aydnzn/Development-of-a-Dorsoventral-Ballistocardiographic-Measurement-System/eagle_docs/fsr_board/3.png

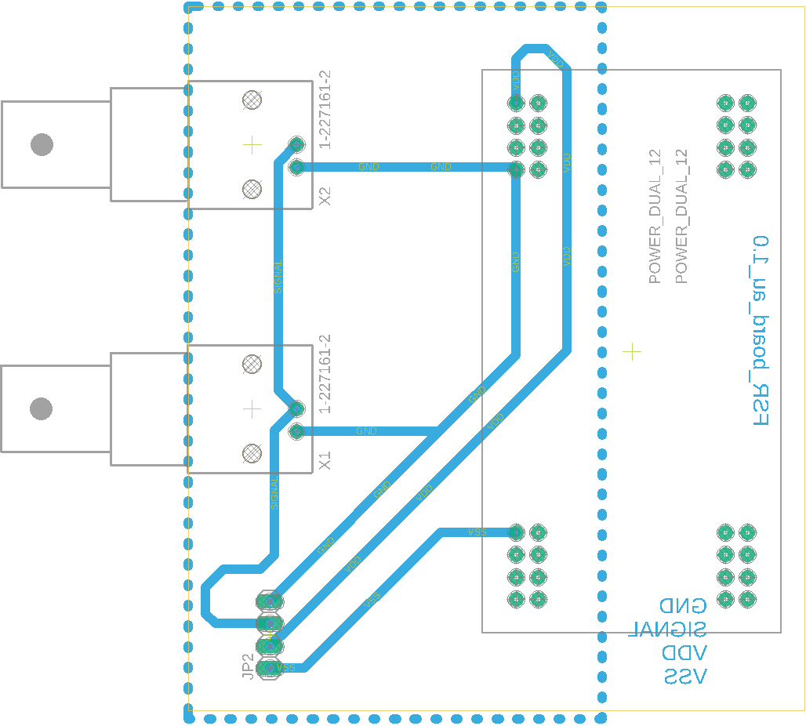
eagle_docs/fsr_board/3.png
