aydnzn/Development-of-a-Dorsoventral-Ballistocardiographic-Measurement-System/eagle_docs/fsr_board/4.png

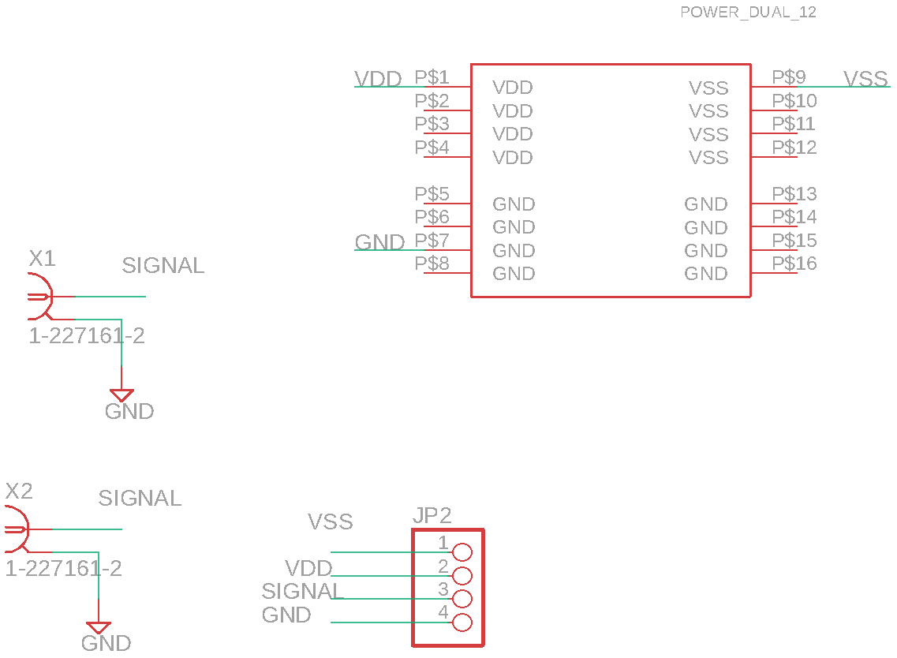
eagle_docs/fsr_board/4.png
