aydnzn/Development-of-a-Dorsoventral-Ballistocardiographic-Measurement-System/eagle_docs/fsr_board/fsr_img.png

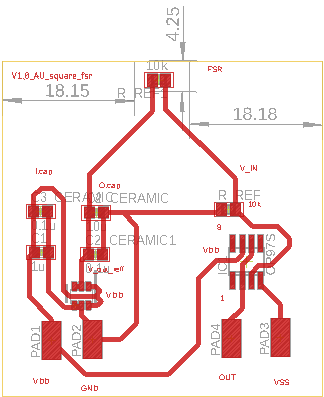
eagle_docs/fsr_board/fsr_img.png
