aydnzn/Development-of-a-Dorsoventral-Ballistocardiographic-Measurement-System/eagle_docs/fsr_board/fsr_sch.png

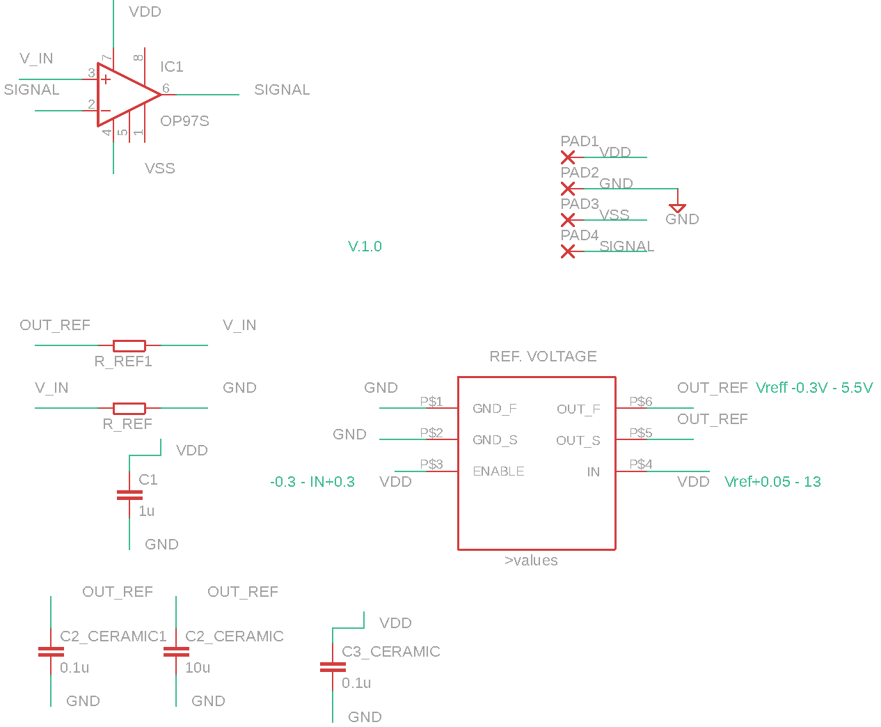
eagle_docs/fsr_board/fsr_sch.png
