aydnzn/Development-of-a-Dorsoventral-Ballistocardiographic-Measurement-System/figs/a_plot_for_rec_043.jpg

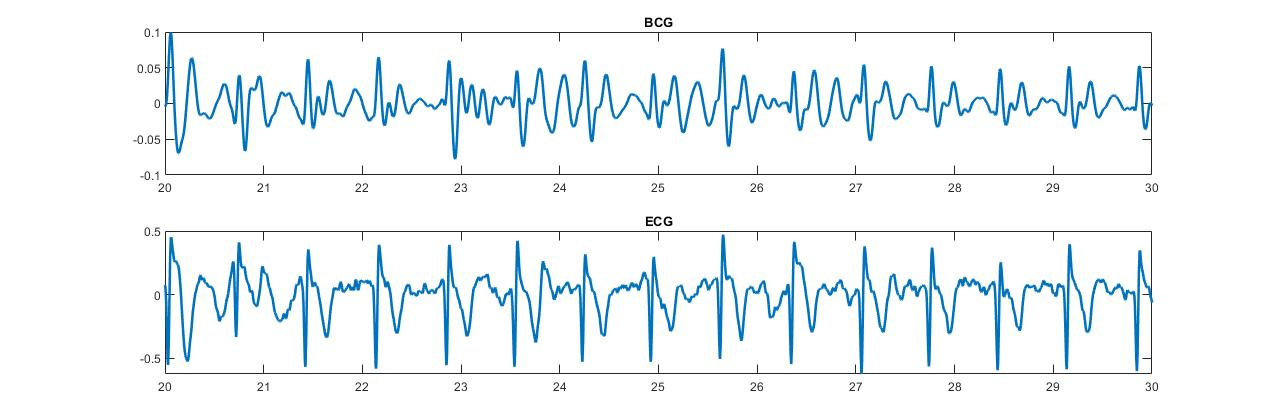
figs/a_plot_for_rec_043.jpg
