aydnzn/Development-of-a-Dorsoventral-Ballistocardiographic-Measurement-System/figs/CM_left_1.1_rec56.jpg

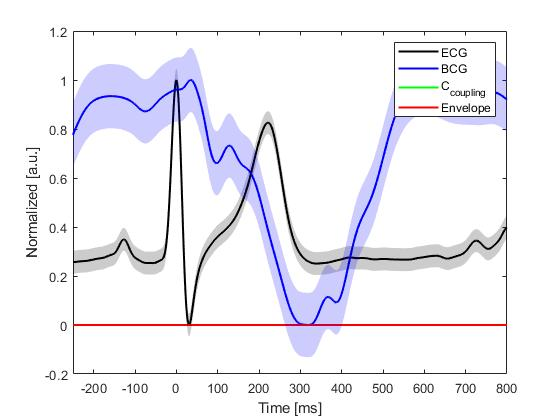
figs/CM_left_1.1_rec56.jpg
