aydnzn/Development-of-a-Dorsoventral-Ballistocardiographic-Measurement-System/figs/CM_left_2.0_xxx.jpg

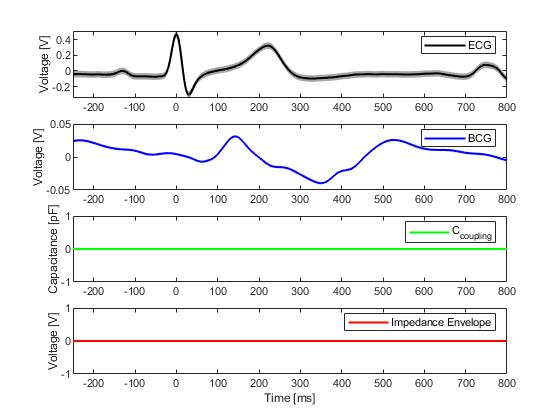
figs/CM_left_2.0_xxx.jpg
