aydnzn/Development-of-a-Dorsoventral-Ballistocardiographic-Measurement-System/figs/CM_left_2.1_xxx.jpg

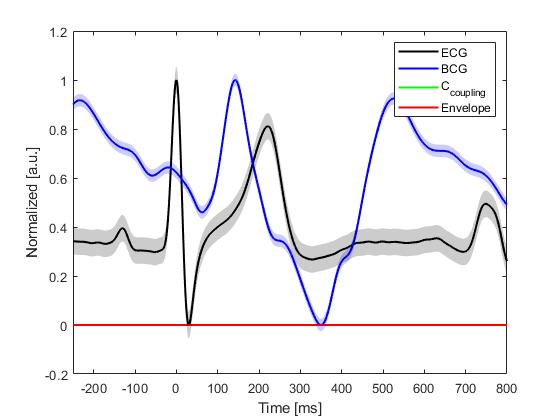
figs/CM_left_2.1_xxx.jpg
