aydnzn/Development-of-a-Dorsoventral-Ballistocardiographic-Measurement-System/figs/CM_left_3.1_rec57.jpg

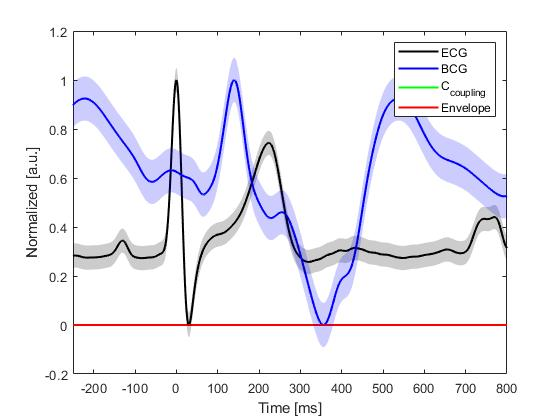
figs/CM_left_3.1_rec57.jpg
