aydnzn/Development-of-a-Dorsoventral-Ballistocardiographic-Measurement-System/figs/CM_left_4.1_rec58.jpg

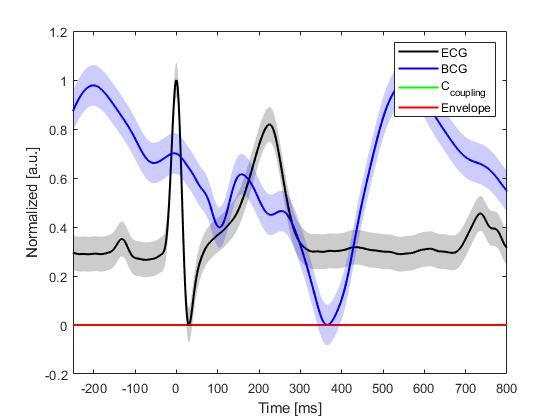
figs/CM_left_4.1_rec58.jpg
