aydnzn/Development-of-a-Dorsoventral-Ballistocardiographic-Measurement-System/figs/CM_right_1.1_rec65.jpg

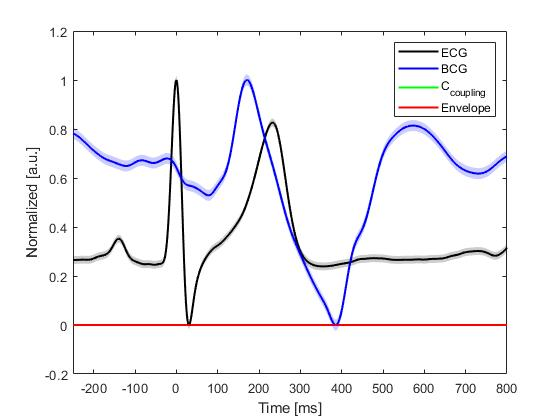
figs/CM_right_1.1_rec65.jpg
