aydnzn/Development-of-a-Dorsoventral-Ballistocardiographic-Measurement-System/figs/CM_right_2.0_rec66.jpg

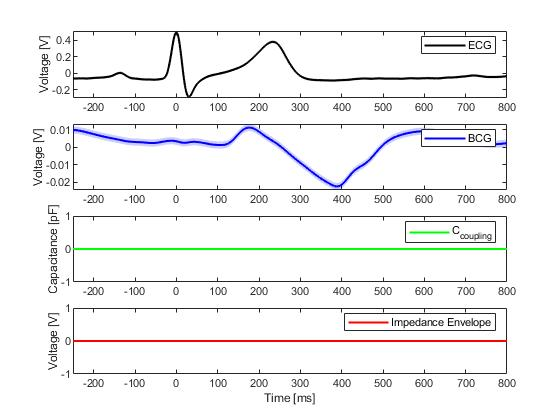
figs/CM_right_2.0_rec66.jpg
