aydnzn/Development-of-a-Dorsoventral-Ballistocardiographic-Measurement-System/figs/CM_right_2.1_rec66.jpg

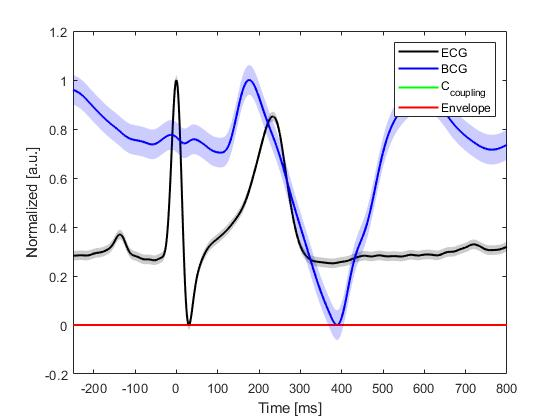
figs/CM_right_2.1_rec66.jpg
