aydnzn/Development-of-a-Dorsoventral-Ballistocardiographic-Measurement-System/figs/CM_right_3.1_rec67.jpg

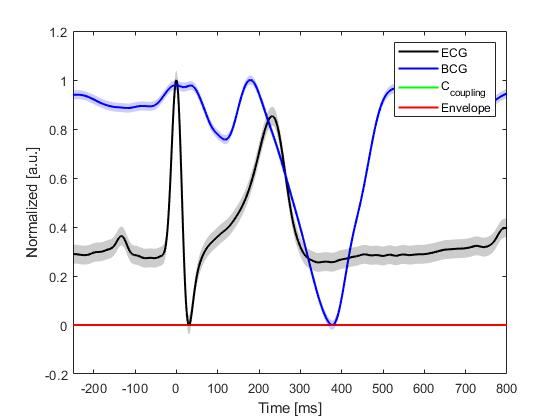
figs/CM_right_3.1_rec67.jpg
