aydnzn/Development-of-a-Dorsoventral-Ballistocardiographic-Measurement-System/figs/dum_1.jpg

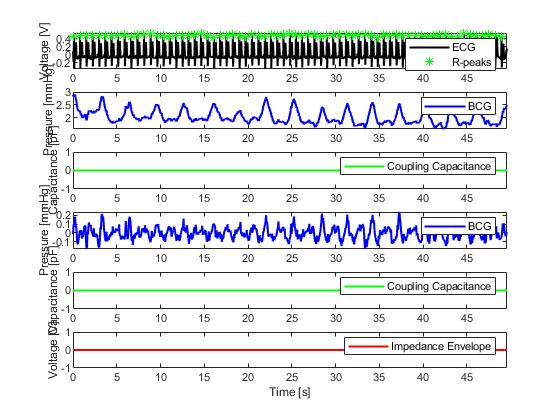
figs/dum_1.jpg
