aydnzn/Development-of-a-Dorsoventral-Ballistocardiographic-Measurement-System/figs/dum_2.jpg

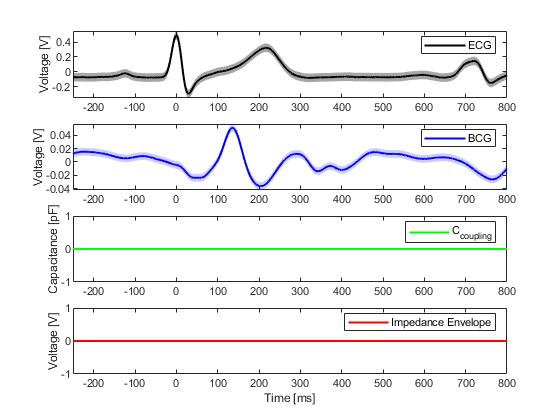
figs/dum_2.jpg
