aydnzn/Development-of-a-Dorsoventral-Ballistocardiographic-Measurement-System/figs/dum_3.jpg

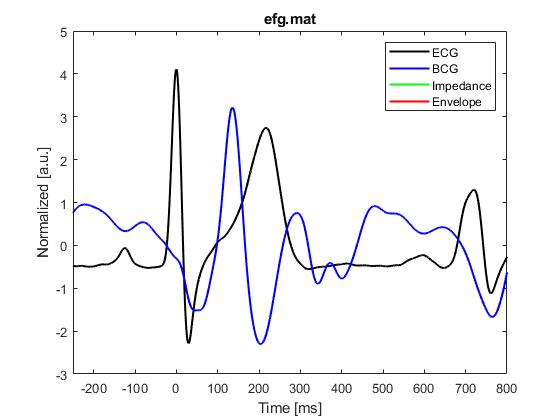
figs/dum_3.jpg
