aydnzn/Development-of-a-Dorsoventral-Ballistocardiographic-Measurement-System/figs/new_filter1.jpg

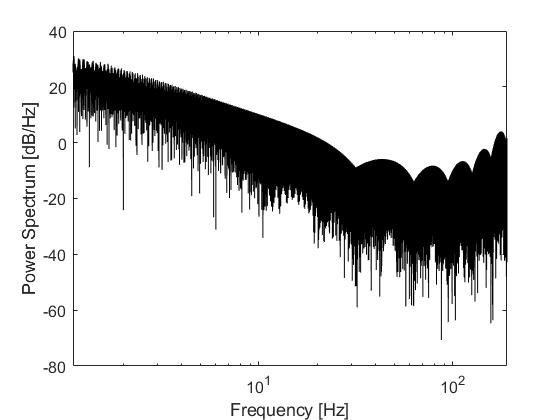
figs/new_filter1.jpg
