aydnzn/Development-of-a-Dorsoventral-Ballistocardiographic-Measurement-System/figs/new_filter2.jpg

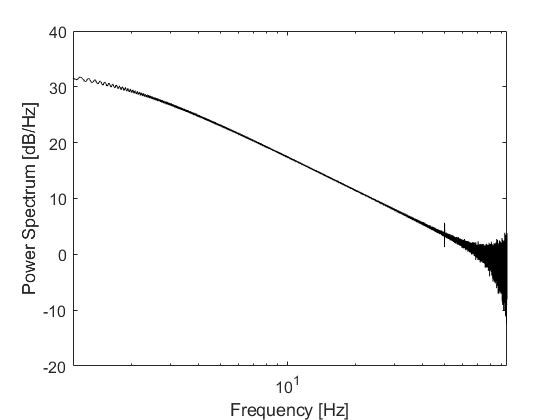
figs/new_filter2.jpg
