aydnzn/Development-of-a-Dorsoventral-Ballistocardiographic-Measurement-System/figs/rec_43.jpg

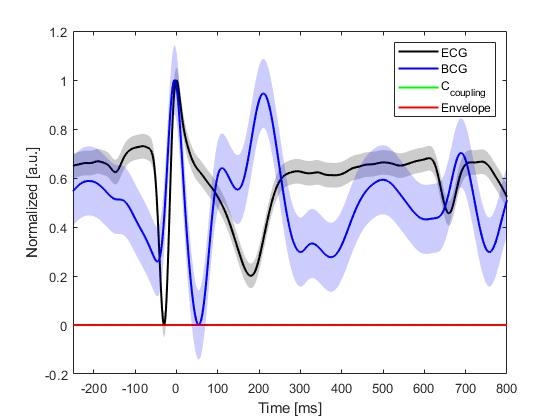
figs/rec_43.jpg
