aydnzn/Development-of-a-Dorsoventral-Ballistocardiographic-Measurement-System/figs/rec_46.jpg

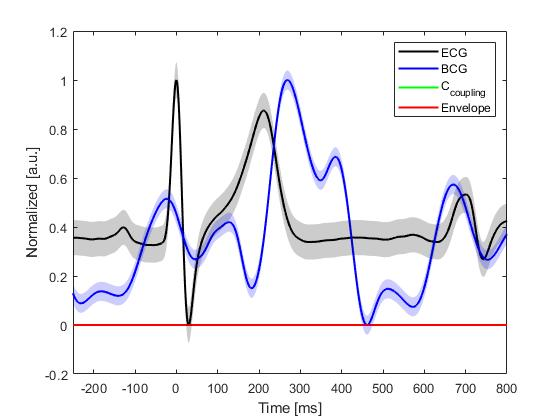
figs/rec_46.jpg
