aydnzn/Development-of-a-Dorsoventral-Ballistocardiographic-Measurement-System/figs/rec_47.jpg

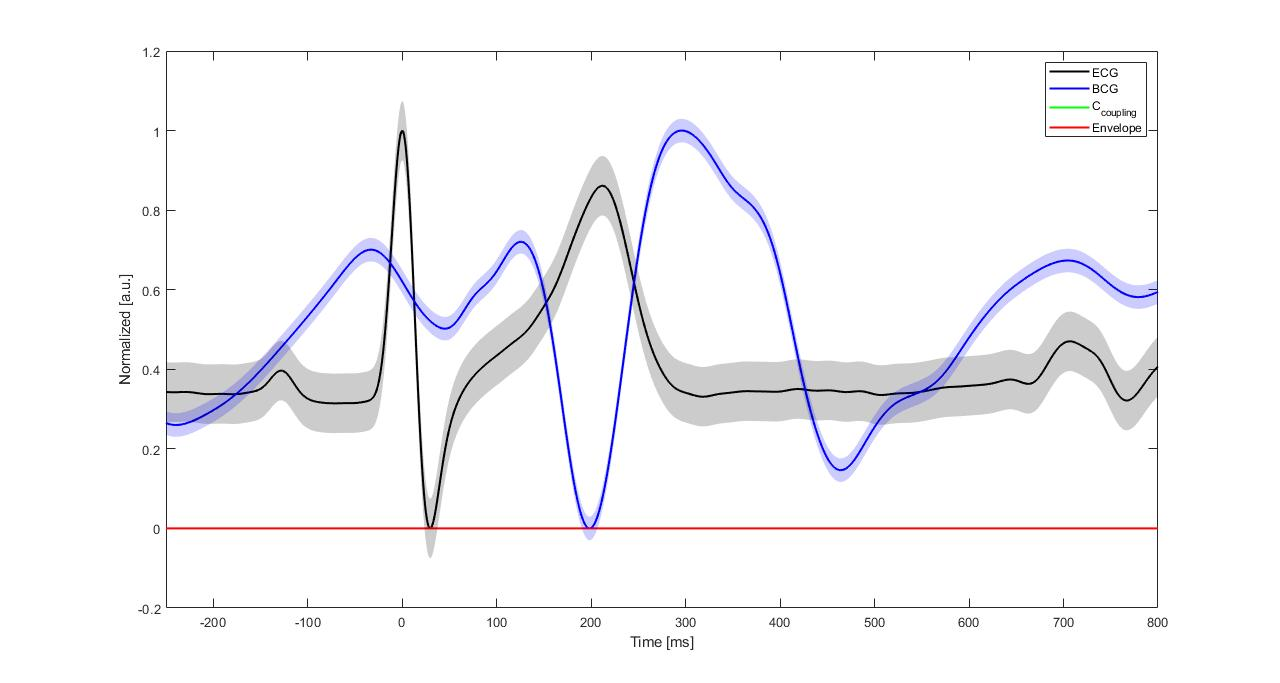
figs/rec_47.jpg
