aydnzn/Development-of-a-Dorsoventral-Ballistocardiographic-Measurement-System/figs/rec_49.jpg

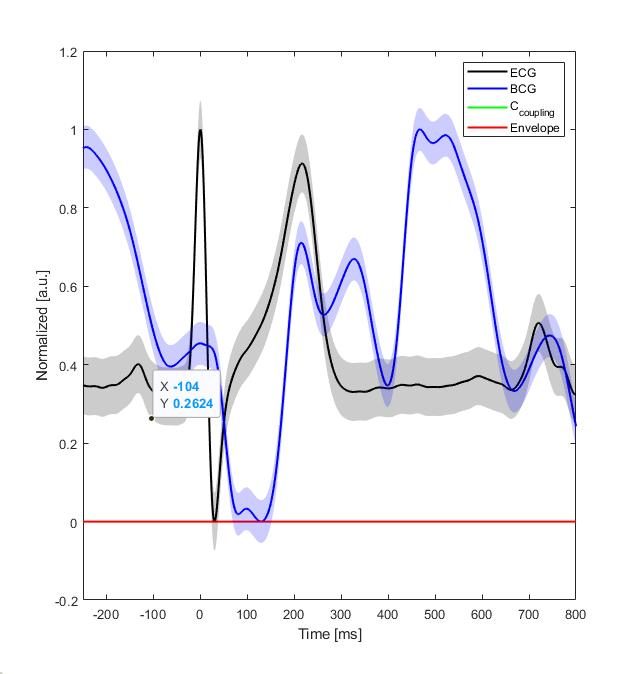
figs/rec_49.jpg
