aydnzn/Development-of-a-Dorsoventral-Ballistocardiographic-Measurement-System/figs/tbt_1.jpg

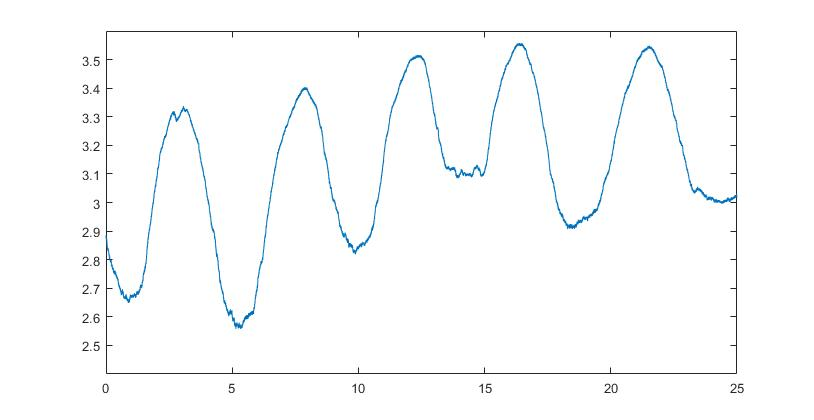
figs/tbt_1.jpg
