aydnzn/Development-of-a-Dorsoventral-Ballistocardiographic-Measurement-System/figs/tbt_2.jpg

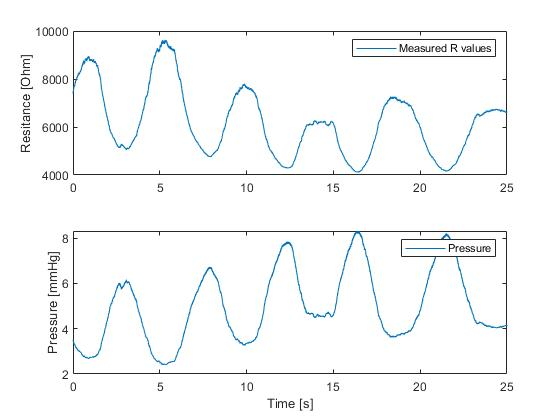
figs/tbt_2.jpg
