aydnzn/Development-of-a-Dorsoventral-Ballistocardiographic-Measurement-System/figs/tbt_3.jpg

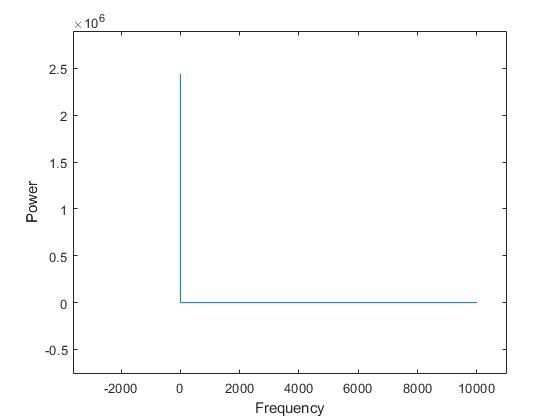
figs/tbt_3.jpg
