aydnzn/Development-of-a-Dorsoventral-Ballistocardiographic-Measurement-System/figs/tbt_4.jpg

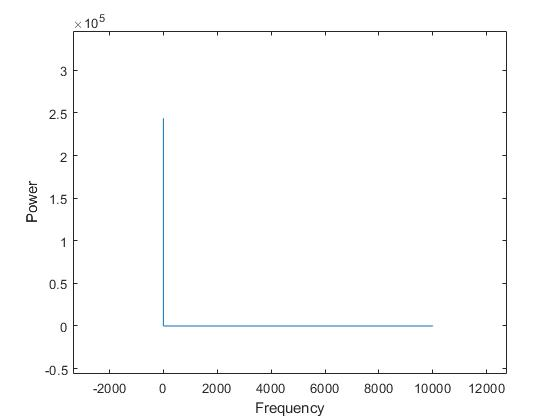
figs/tbt_4.jpg
