aydnzn/Development-of-a-Dorsoventral-Ballistocardiographic-Measurement-System/figs/tbt_5.jpg

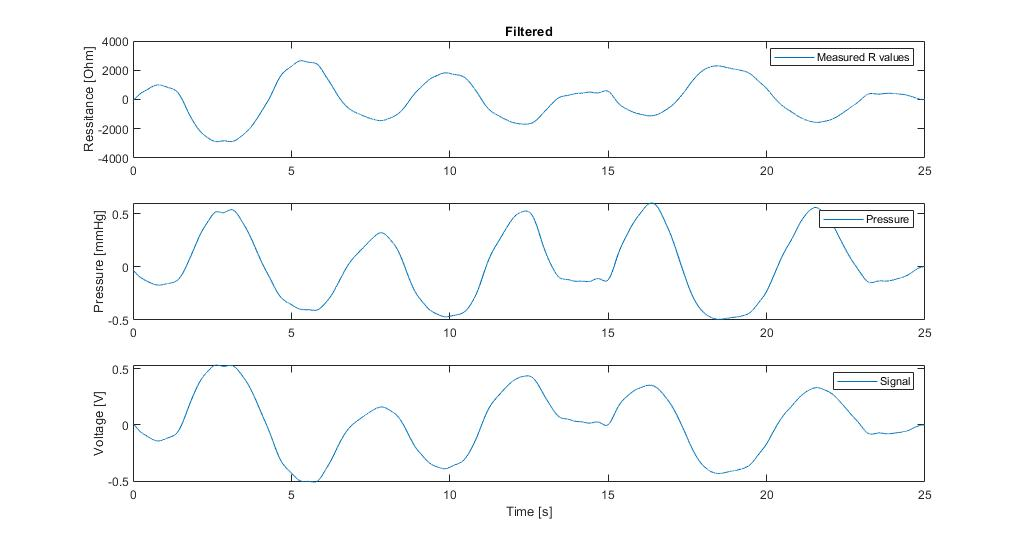
figs/tbt_5.jpg
