aydnzn/Development-of-a-Dorsoventral-Ballistocardiographic-Measurement-System/figs/tbt_6.jpg

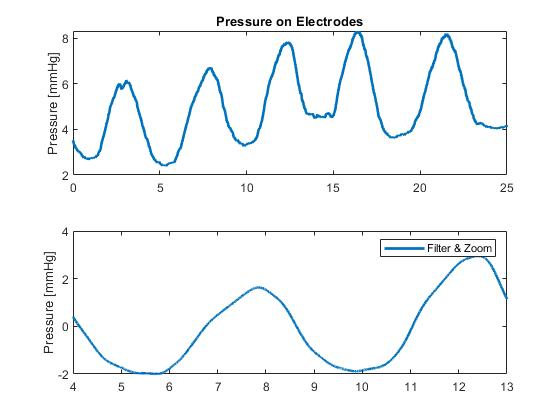
figs/tbt_6.jpg
