aydnzn/Development-of-a-Dorsoventral-Ballistocardiographic-Measurement-System/figs/uu_2.jpg

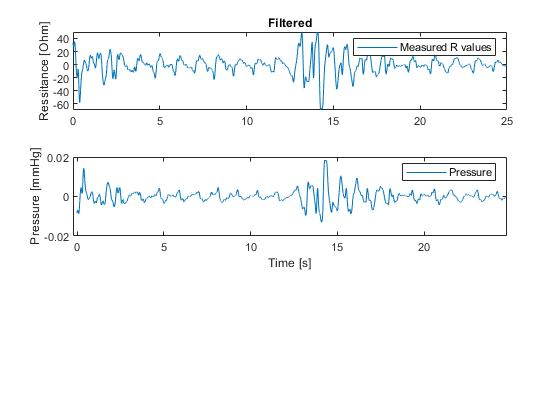
figs/uu_2.jpg
