aydnzn/Development-of-a-Dorsoventral-Ballistocardiographic-Measurement-System/figs/uu_3.jpg

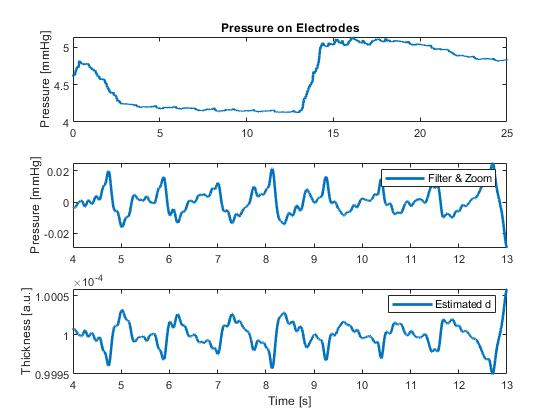
figs/uu_3.jpg
