aydnzn/Development-of-a-Dorsoventral-Ballistocardiographic-Measurement-System/figs/VM_left_1.0_rec50.jpg

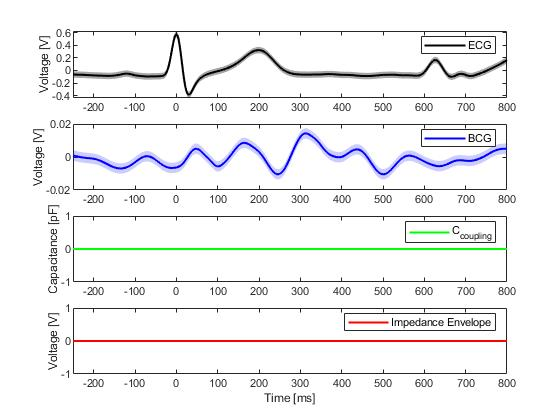
figs/VM_left_1.0_rec50.jpg
