aydnzn/Development-of-a-Dorsoventral-Ballistocardiographic-Measurement-System/figs/VM_left_2.0_rec51.jpg

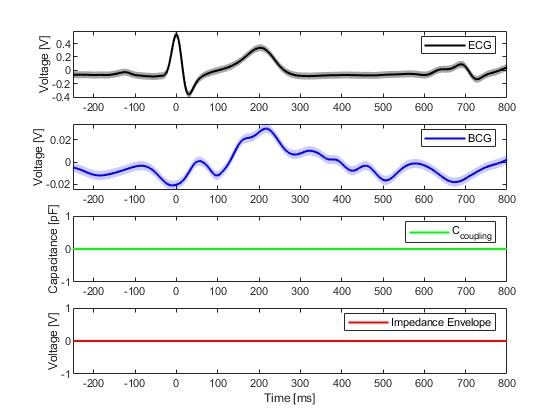
figs/VM_left_2.0_rec51.jpg
