aydnzn/Development-of-a-Dorsoventral-Ballistocardiographic-Measurement-System/figs/VM_left_3.1_xxx.jpg

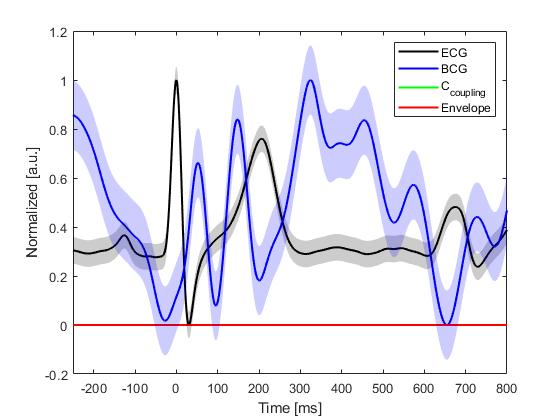
figs/VM_left_3.1_xxx.jpg
