aydnzn/Development-of-a-Dorsoventral-Ballistocardiographic-Measurement-System/figs/VM_left_4.1_rec52.jpg

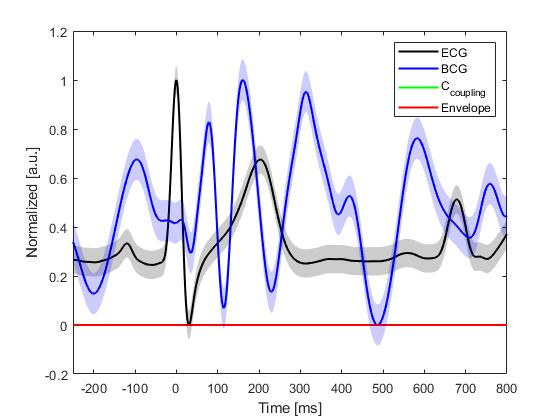
figs/VM_left_4.1_rec52.jpg
