aydnzn/Development-of-a-Dorsoventral-Ballistocardiographic-Measurement-System/figs/VM_left_5.1_rec53.jpg

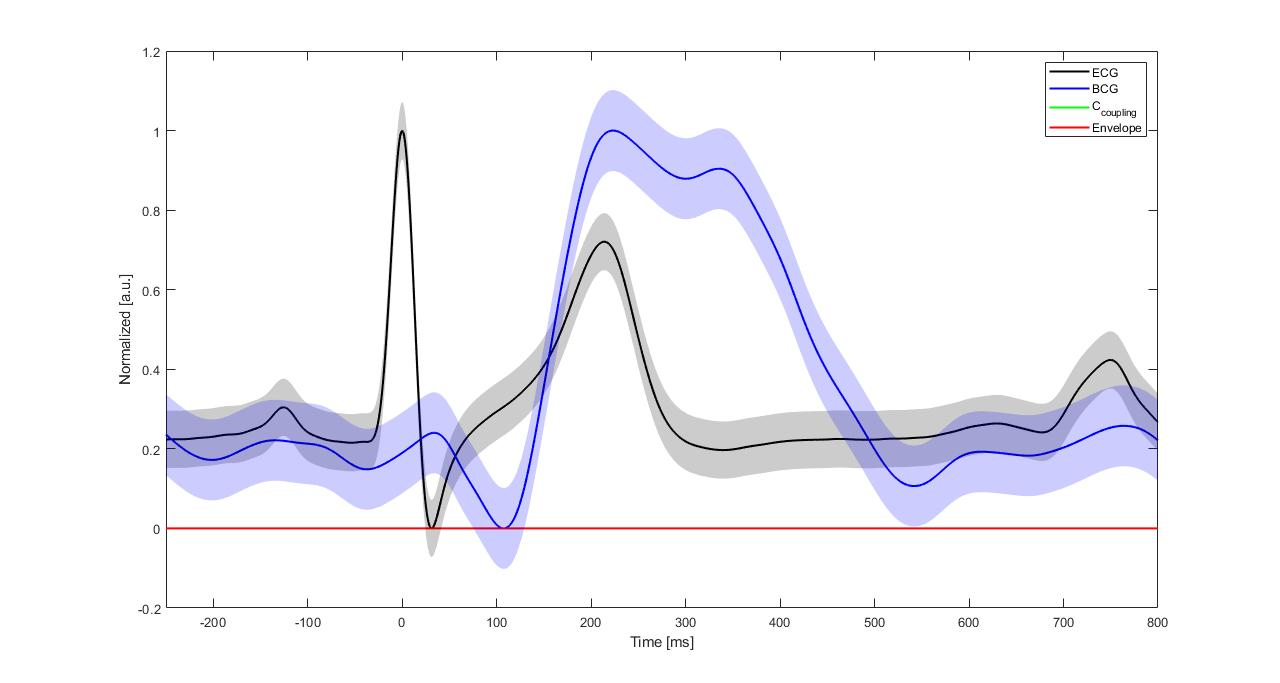
figs/VM_left_5.1_rec53.jpg
