aydnzn/Development-of-a-Dorsoventral-Ballistocardiographic-Measurement-System/figs/VM_left_hip.1.1_xxx.jpg

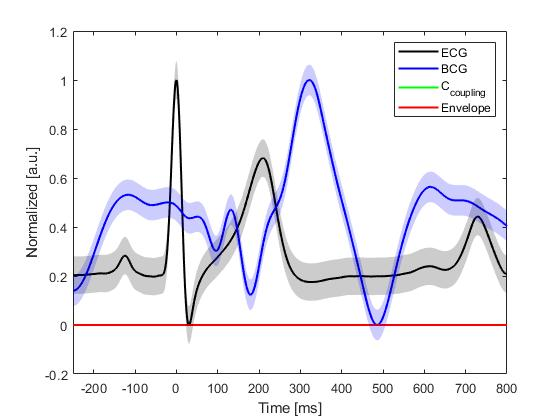
figs/VM_left_hip.1.1_xxx.jpg
