aydnzn/Development-of-a-Dorsoventral-Ballistocardiographic-Measurement-System/figs/VM_right_1.1_rec59.jpg

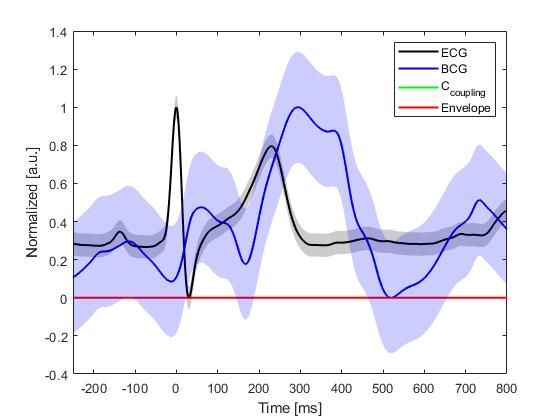
figs/VM_right_1.1_rec59.jpg
