aydnzn/Development-of-a-Dorsoventral-Ballistocardiographic-Measurement-System/figs/VM_right_2.1_rec60.jpg

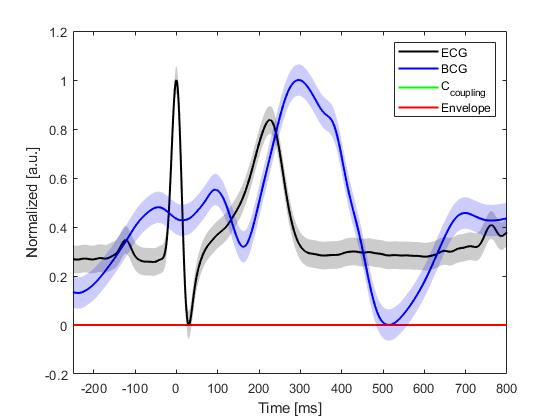
figs/VM_right_2.1_rec60.jpg
