aydnzn/Development-of-a-Dorsoventral-Ballistocardiographic-Measurement-System/figs/VM_right_4.1_xxx.jpg

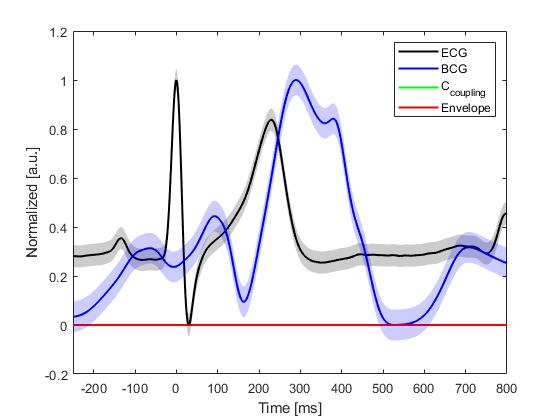
figs/VM_right_4.1_xxx.jpg
