aydnzn/Development-of-a-Dorsoventral-Ballistocardiographic-Measurement-System/figs/VM_right_hip.1.0_rec62.jpg

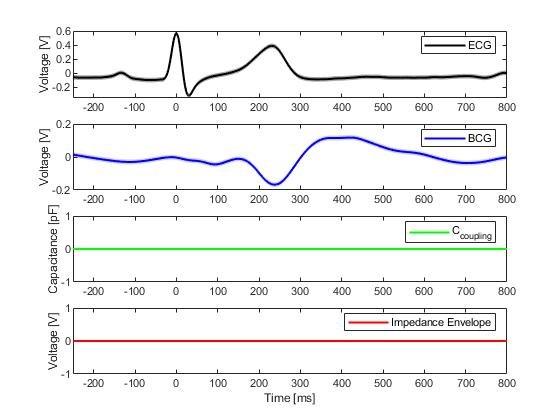
figs/VM_right_hip.1.0_rec62.jpg
