aydnzn/Development-of-a-Dorsoventral-Ballistocardiographic-Measurement-System/figs/VM_right_hip.2.1_rec63.jpg

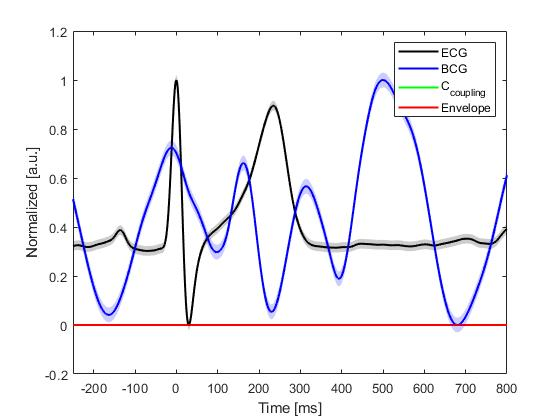
figs/VM_right_hip.2.1_rec63.jpg
