aydnzn/Development-of-a-Dorsoventral-Ballistocardiographic-Measurement-System/photos/bottom_sensing_unit.png

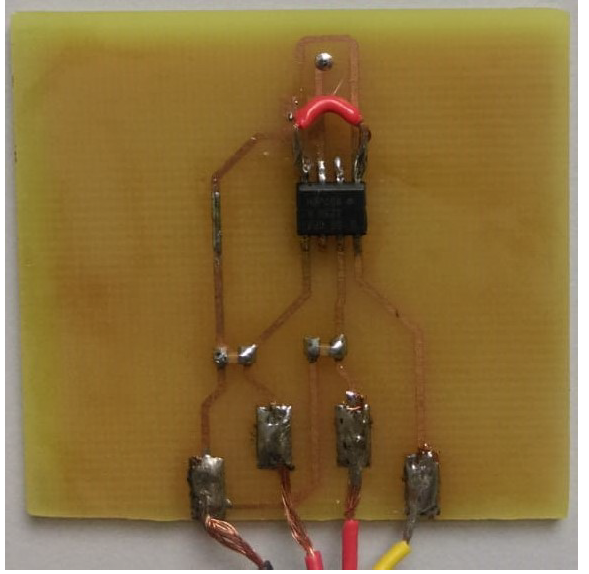
photos/bottom_sensing_unit.png
