aydnzn/Development-of-a-Dorsoventral-Ballistocardiographic-Measurement-System/photos/CNC_machine_production.jpeg

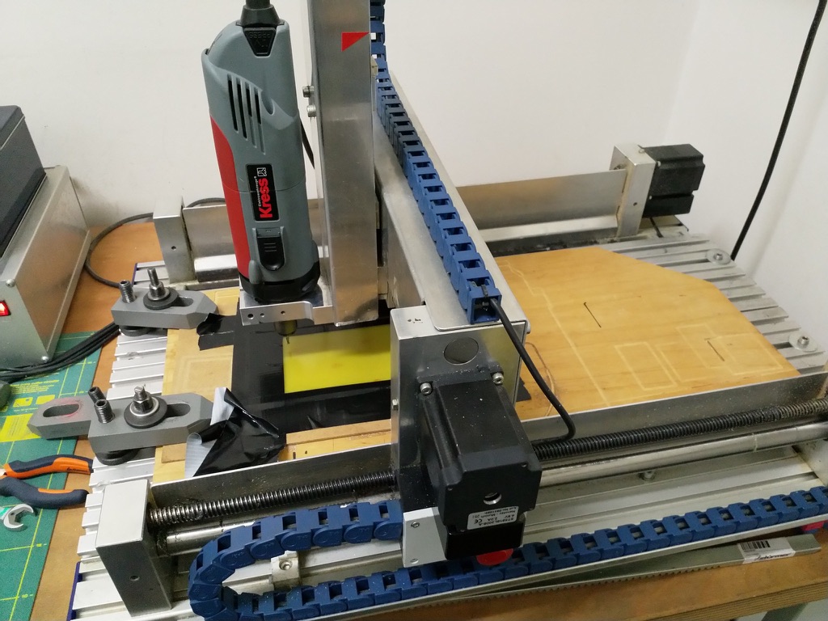
photos/CNC_machine_production.jpeg
