aydnzn/Development-of-a-Dorsoventral-Ballistocardiographic-Measurement-System/photos/CNC_machine_production_2.jpeg

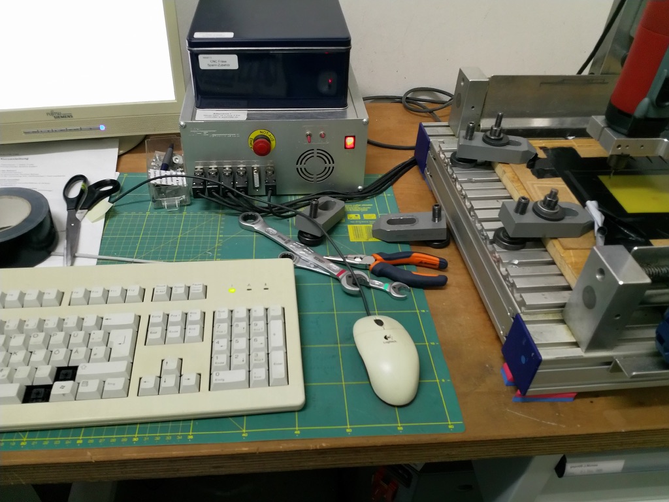
photos/CNC_machine_production_2.jpeg
