aydnzn/Development-of-a-Dorsoventral-Ballistocardiographic-Measurement-System/photos/conductive_office_chair.png

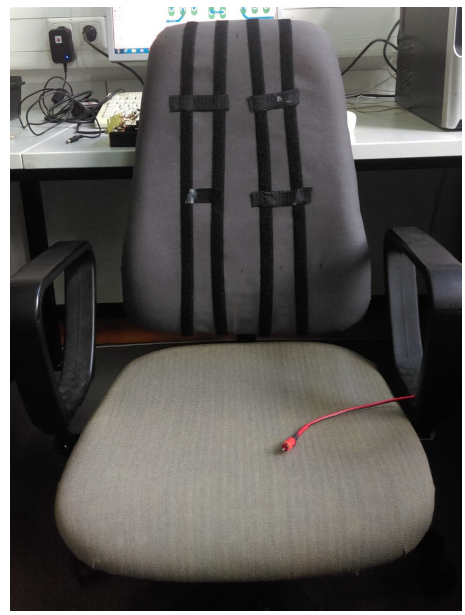
photos/conductive_office_chair.png
