aydnzn/Development-of-a-Dorsoventral-Ballistocardiographic-Measurement-System/photos/EAGLE.jpeg

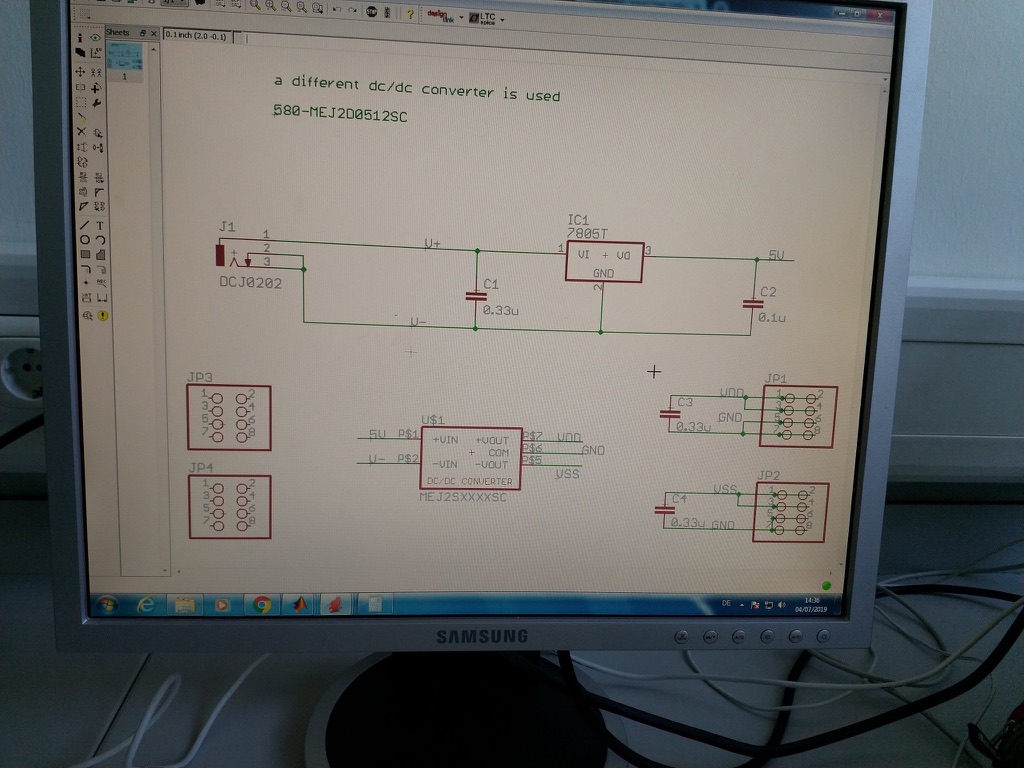
photos/EAGLE.jpeg
