aydnzn/Development-of-a-Dorsoventral-Ballistocardiographic-Measurement-System/photos/EAGLE_2.jpeg

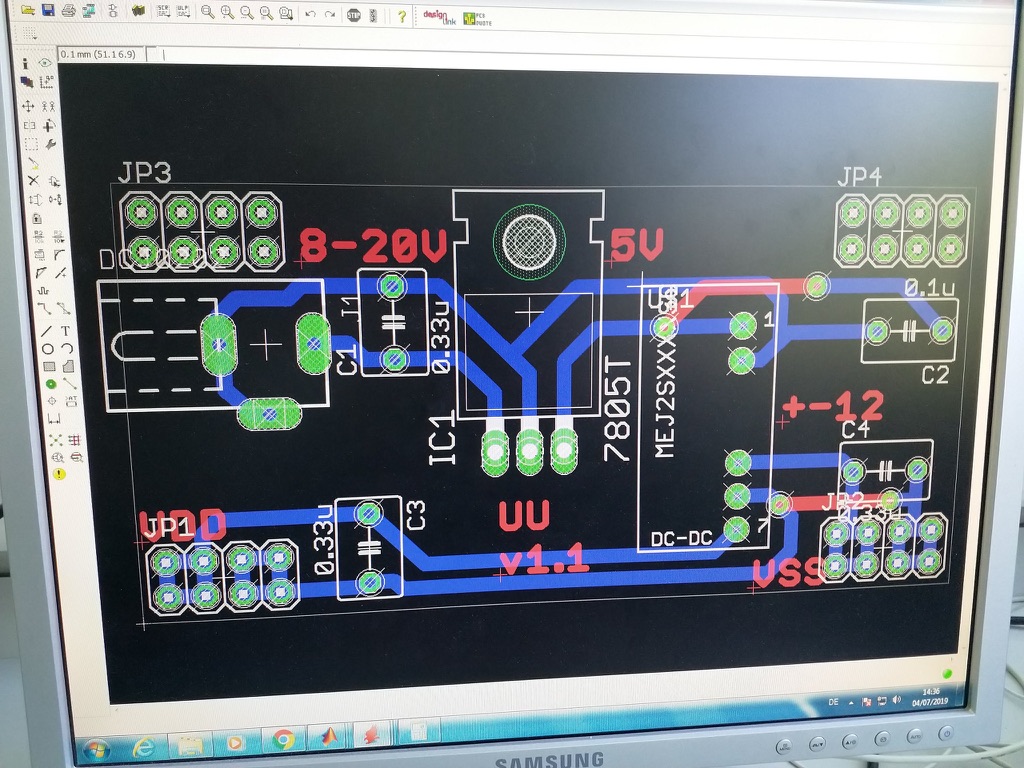
photos/EAGLE_2.jpeg
