aydnzn/Development-of-a-Dorsoventral-Ballistocardiographic-Measurement-System/photos/etching_room.jpeg

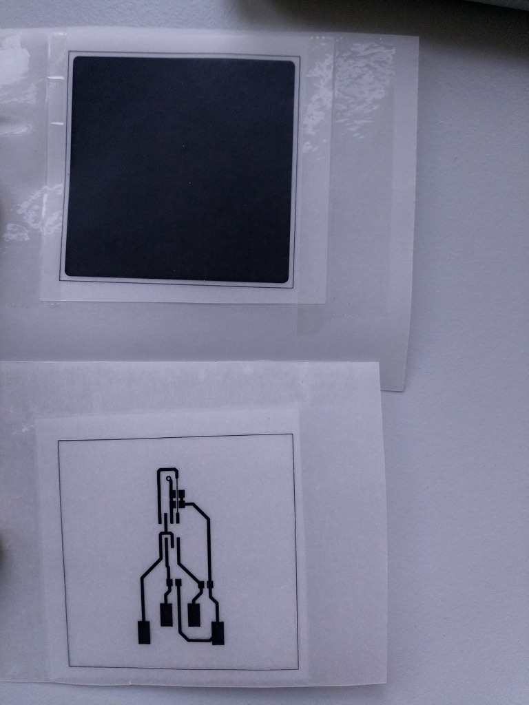
photos/etching_room.jpeg
