aydnzn/Development-of-a-Dorsoventral-Ballistocardiographic-Measurement-System/photos/etching_room_2.jpeg

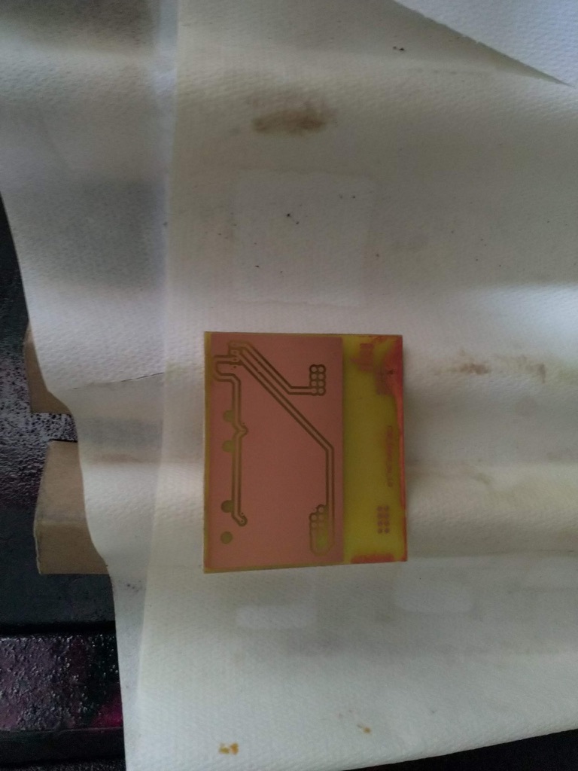
photos/etching_room_2.jpeg
