aydnzn/Development-of-a-Dorsoventral-Ballistocardiographic-Measurement-System/photos/etching_room_3.jpeg

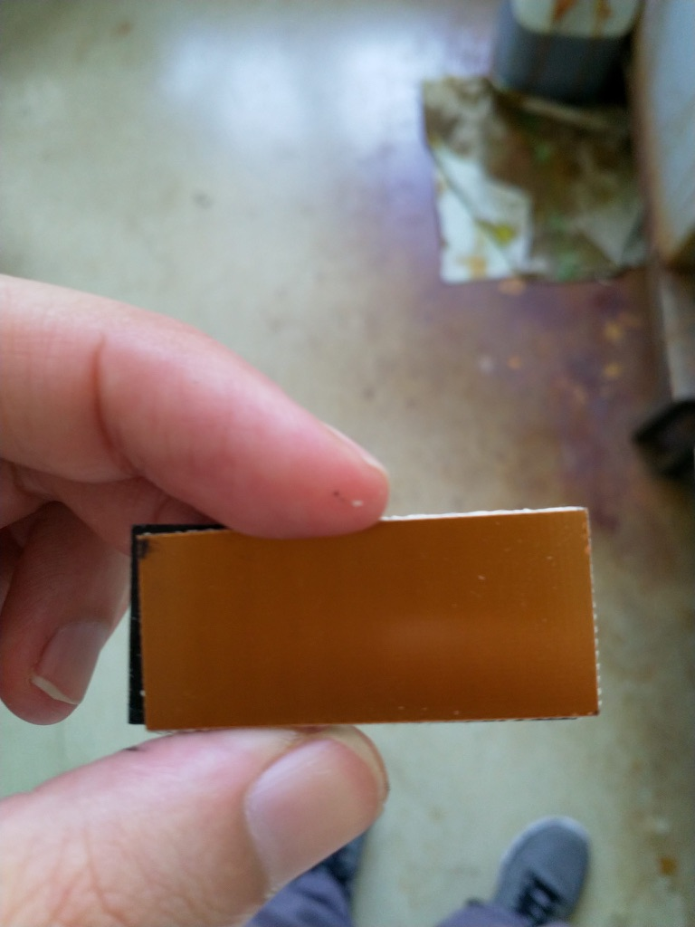
photos/etching_room_3.jpeg
