aydnzn/Development-of-a-Dorsoventral-Ballistocardiographic-Measurement-System/photos/filtering_module.png

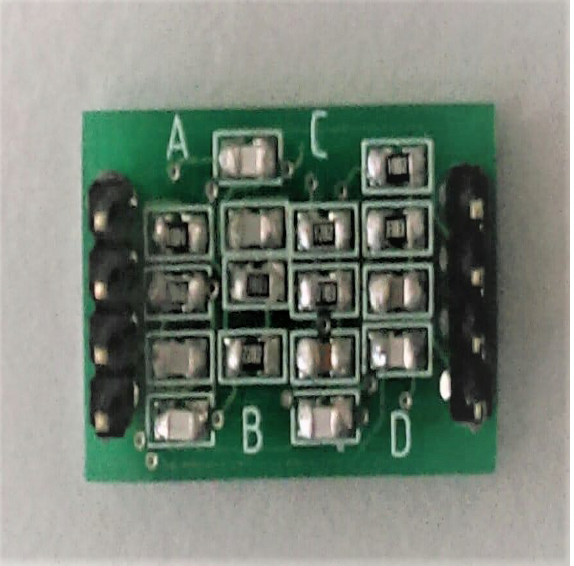
photos/filtering_module.png
