aydnzn/Development-of-a-Dorsoventral-Ballistocardiographic-Measurement-System/photos/filtering_module_2.png

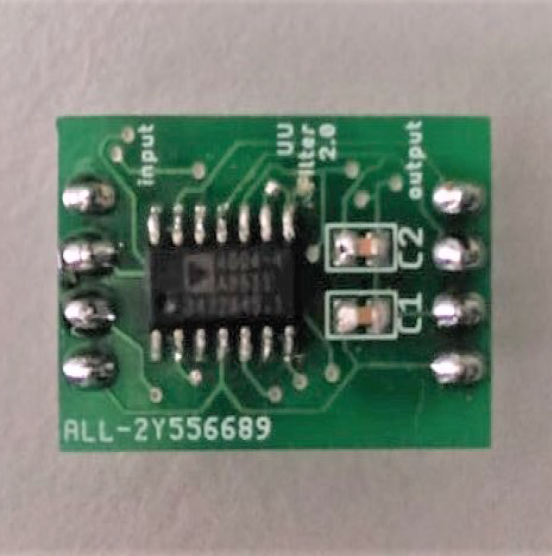
photos/filtering_module_2.png
