aydnzn/Development-of-a-Dorsoventral-Ballistocardiographic-Measurement-System/photos/NI.jpeg

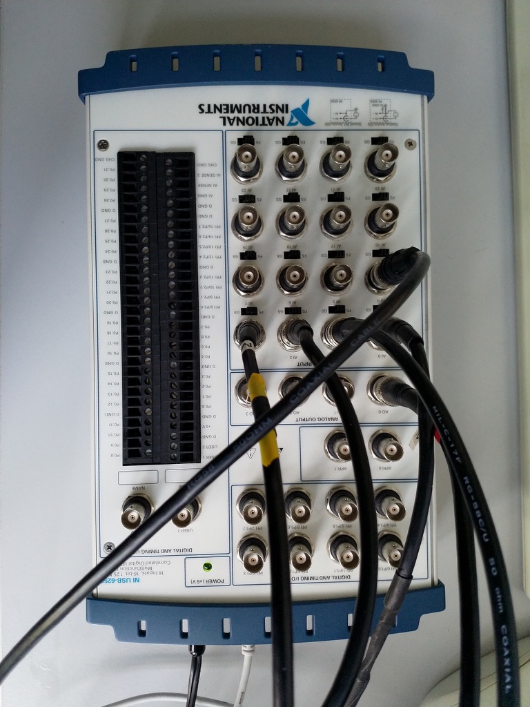
photos/NI.jpeg
