aydnzn/Development-of-a-Dorsoventral-Ballistocardiographic-Measurement-System/photos/NI_2.jpeg

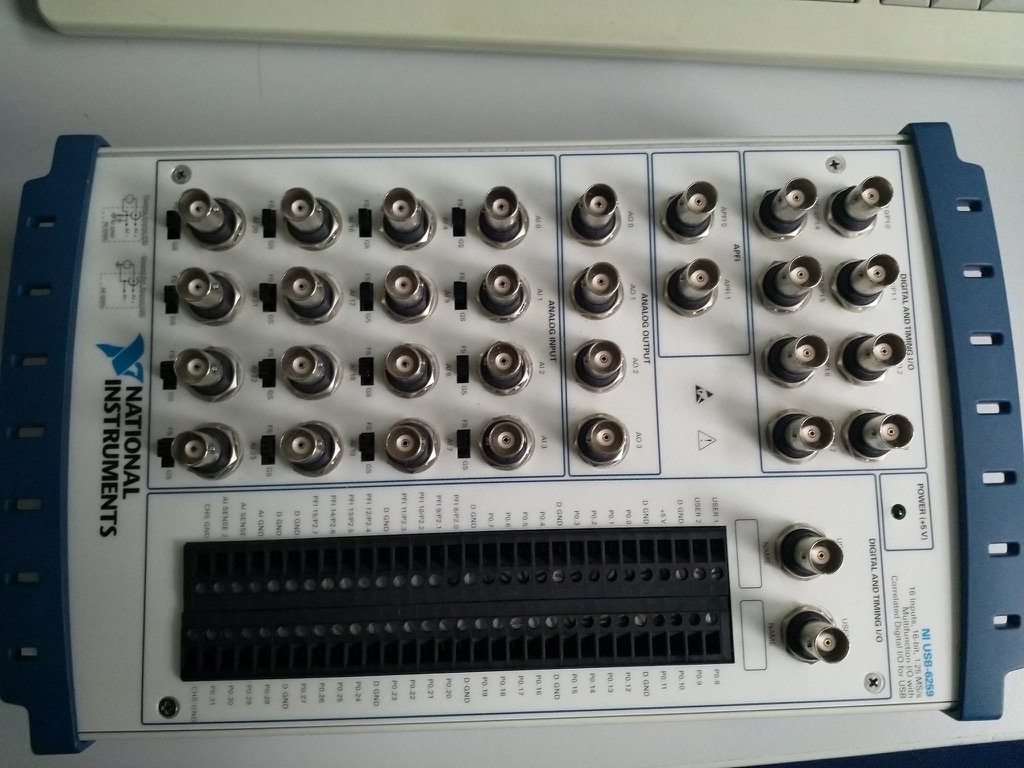
photos/NI_2.jpeg
