aydnzn/Development-of-a-Dorsoventral-Ballistocardiographic-Measurement-System/photos/sensing_unit.jpeg

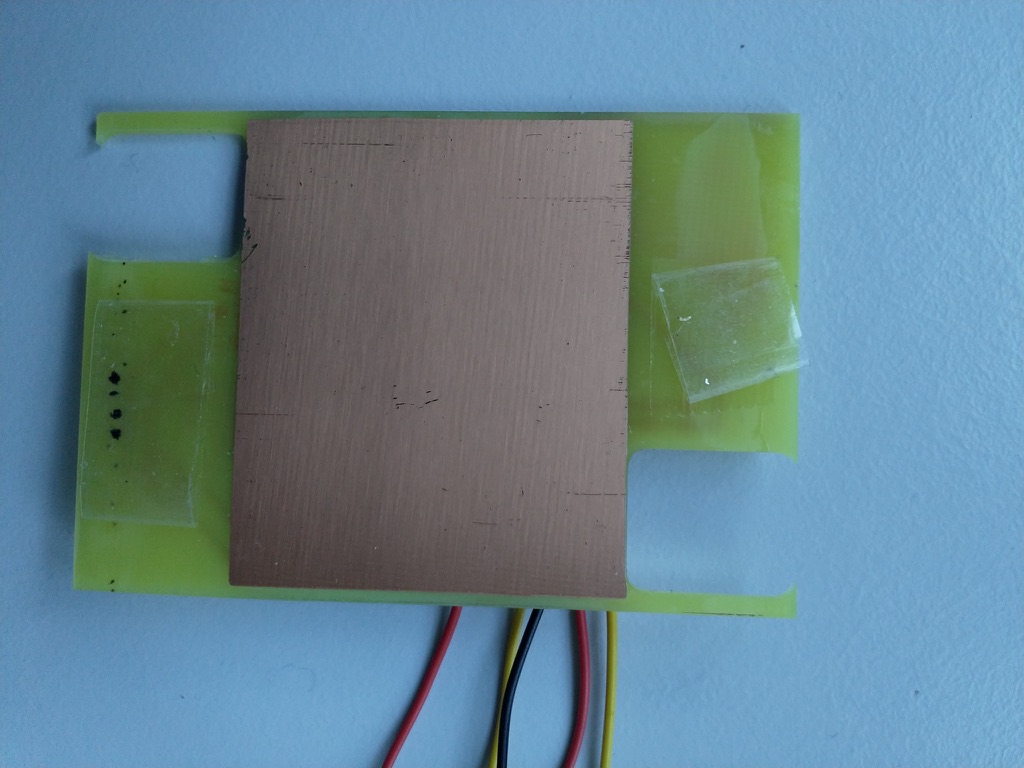
photos/sensing_unit.jpeg
