aydnzn/Development-of-a-Dorsoventral-Ballistocardiographic-Measurement-System/photos/Sensing_unit_and_PVDF_sensor.png

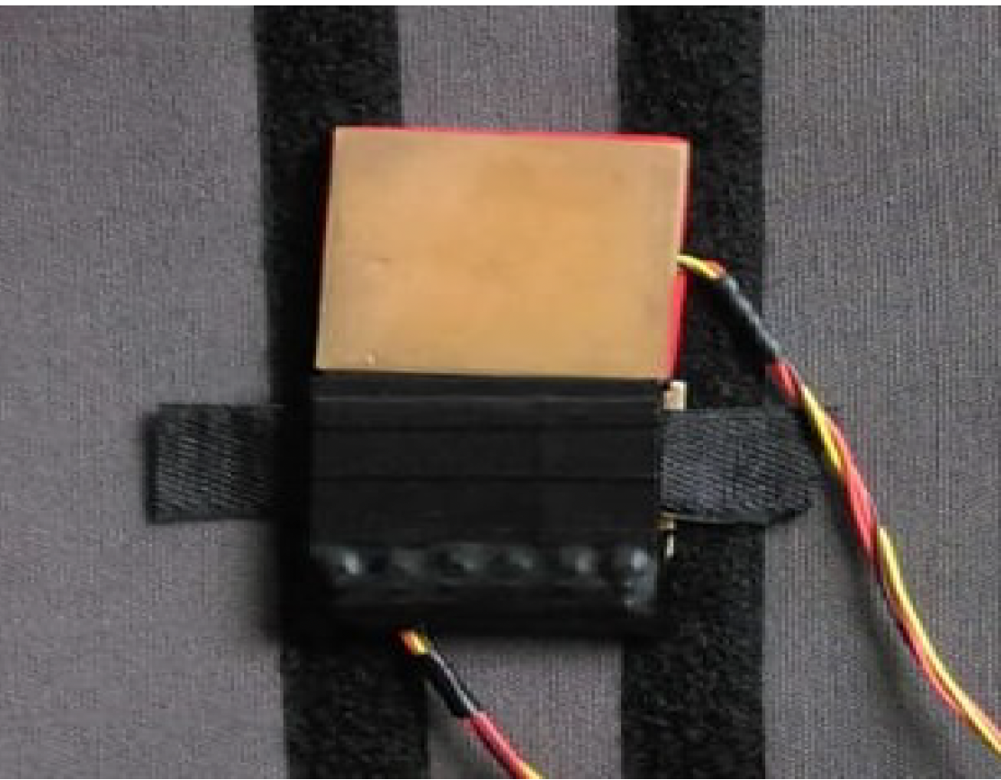
photos/Sensing_unit_and_PVDF_sensor.png
