aydnzn/Development-of-a-Dorsoventral-Ballistocardiographic-Measurement-System/photos/sensor_main_board.jpeg

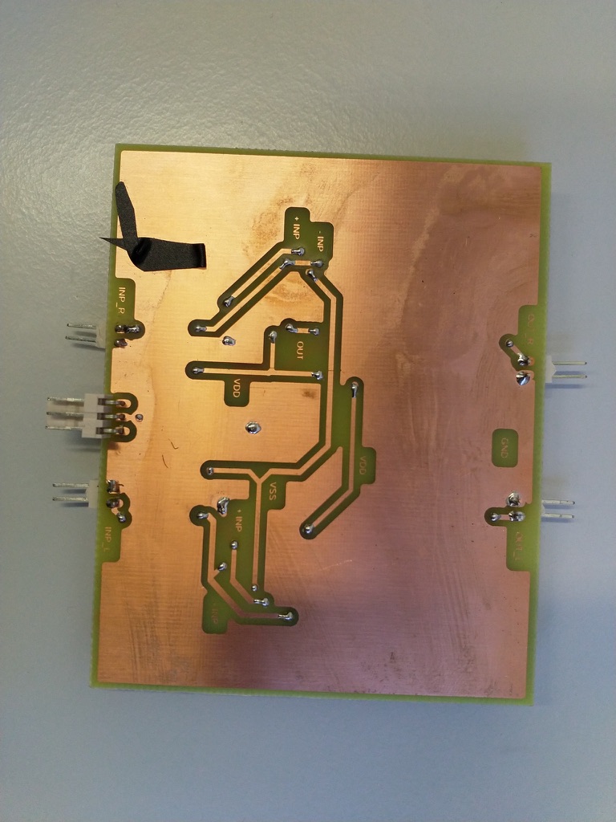
photos/sensor_main_board.jpeg
