aydnzn/Development-of-a-Dorsoventral-Ballistocardiographic-Measurement-System/photos/sensor_main_board_9.jpeg

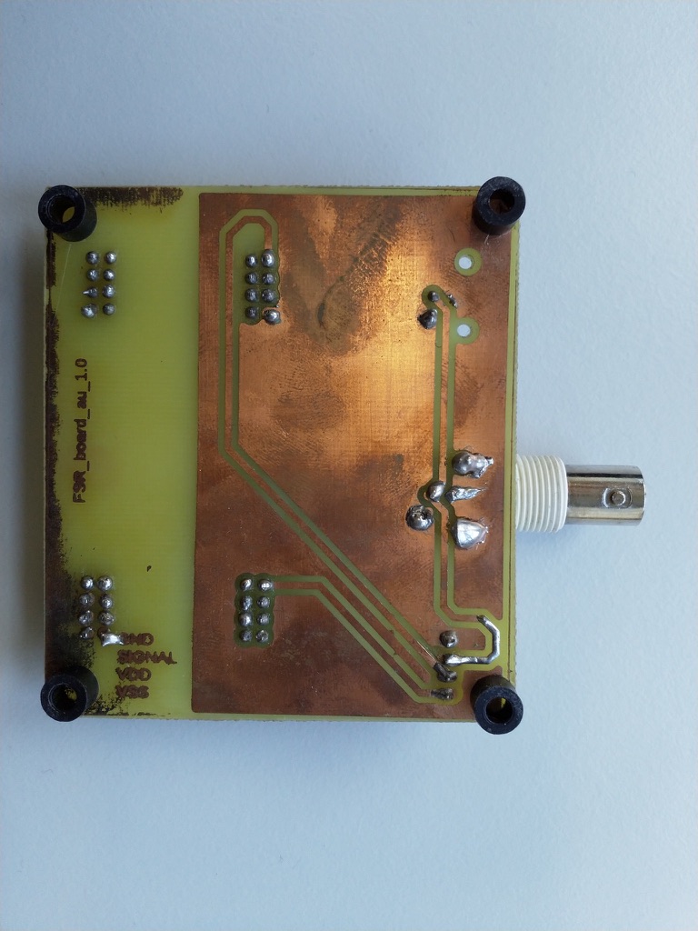
photos/sensor_main_board_9.jpeg
