aydnzn/Development-of-a-Dorsoventral-Ballistocardiographic-Measurement-System/photos/sensor_main_board_10.jpeg

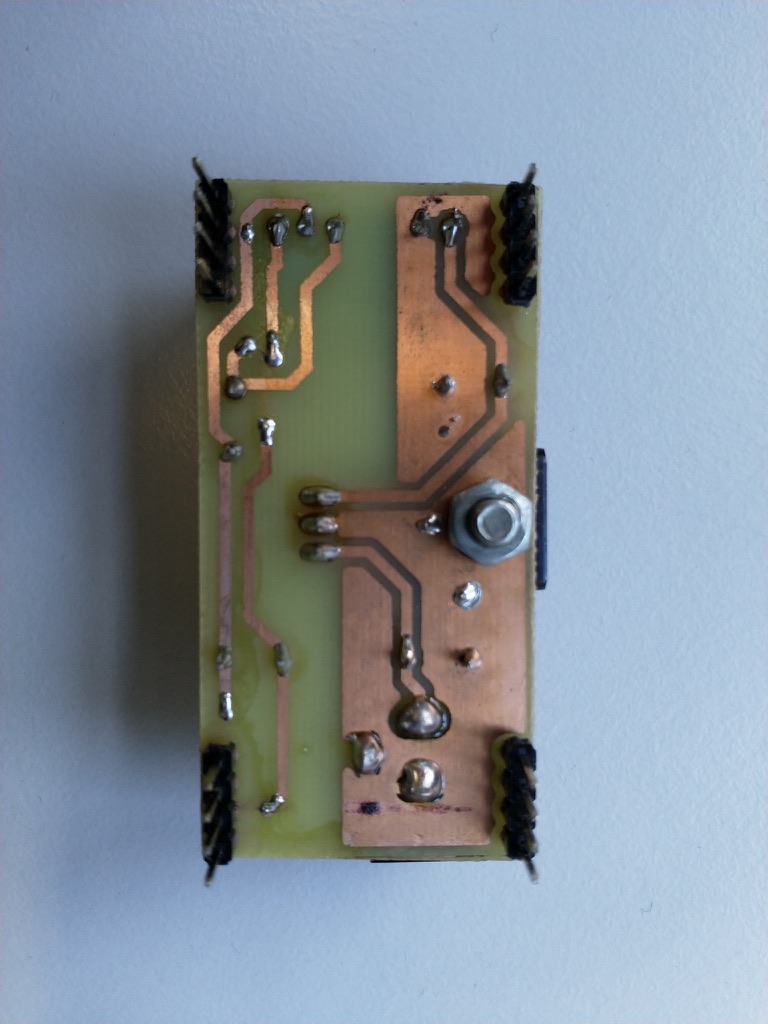
photos/sensor_main_board_10.jpeg
