aydnzn/Development-of-a-Dorsoventral-Ballistocardiographic-Measurement-System/photos/top_sensing_unit.png

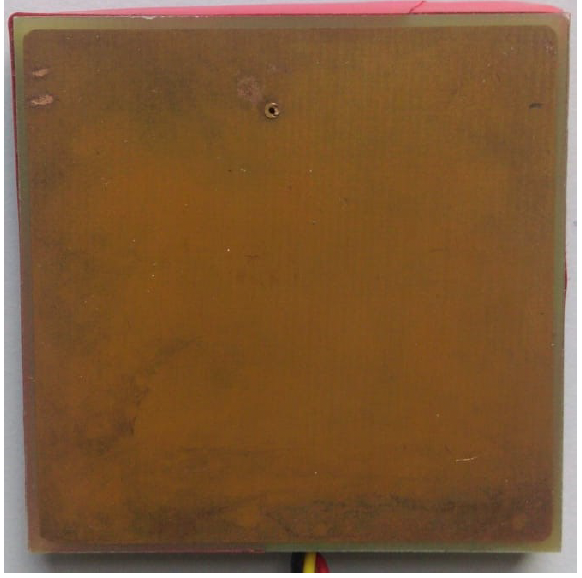
photos/top_sensing_unit.png
