aydnzn/Development-of-a-Dorsoventral-Ballistocardiographic-Measurement-System/photos/Voltage_supply.jpeg

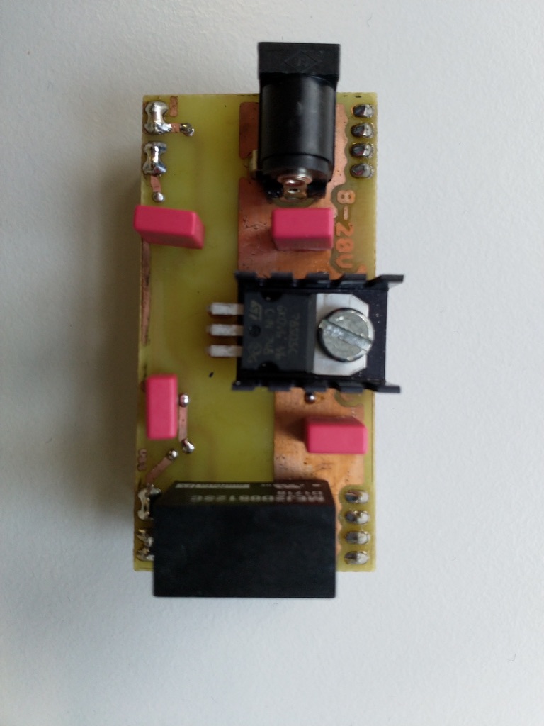
photos/Voltage_supply.jpeg
