aydnzn/Development-of-a-Dorsoventral-Ballistocardiographic-Measurement-System/photos/Voltage_supply_2.jpeg

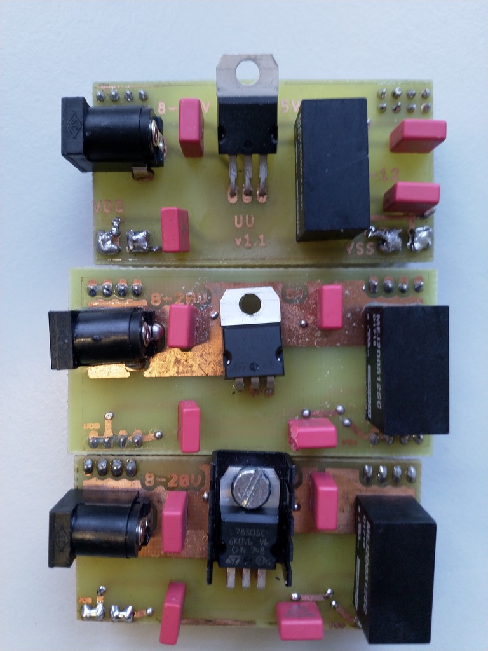
photos/Voltage_supply_2.jpeg
