aydnzn/Development-of-a-Dorsoventral-Ballistocardiographic-Measurement-System/photos/soldering_lab.jpeg

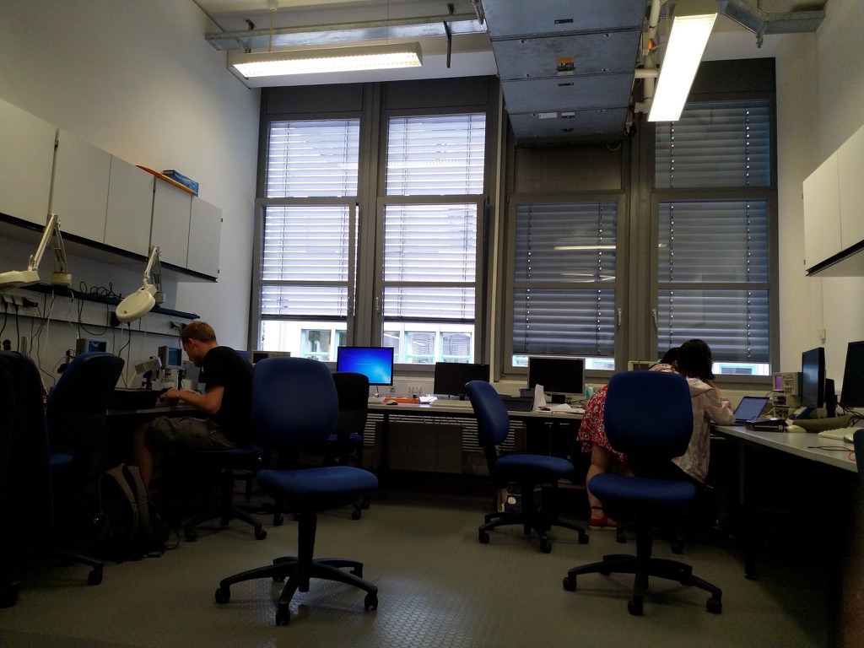
photos/soldering_lab.jpeg
