aydnzn/Development-of-a-Dorsoventral-Ballistocardiographic-Measurement-System/photos/soldering_lab_2.jpeg

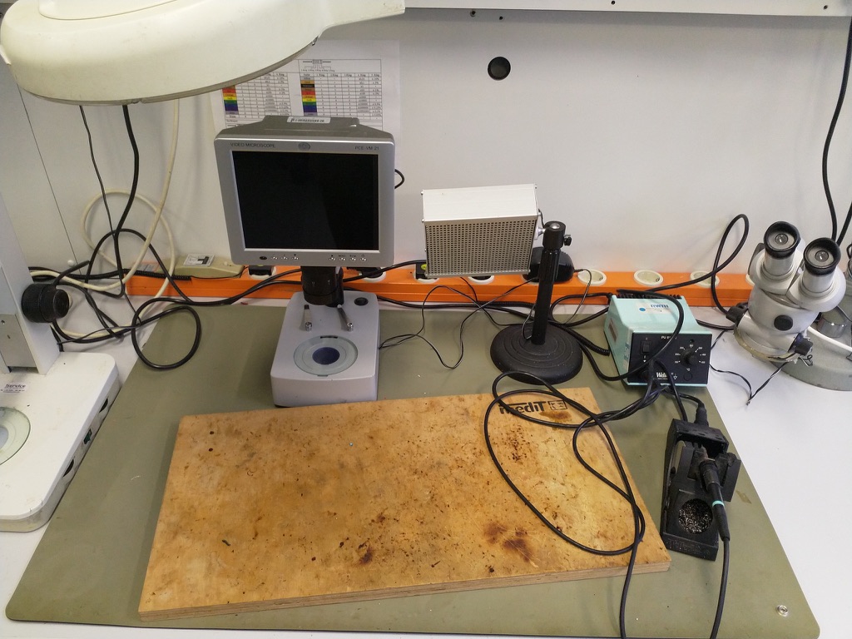
photos/soldering_lab_2.jpeg
