aydnzn/Development-of-a-Dorsoventral-Ballistocardiographic-Measurement-System/photos/measurement_box.jpeg

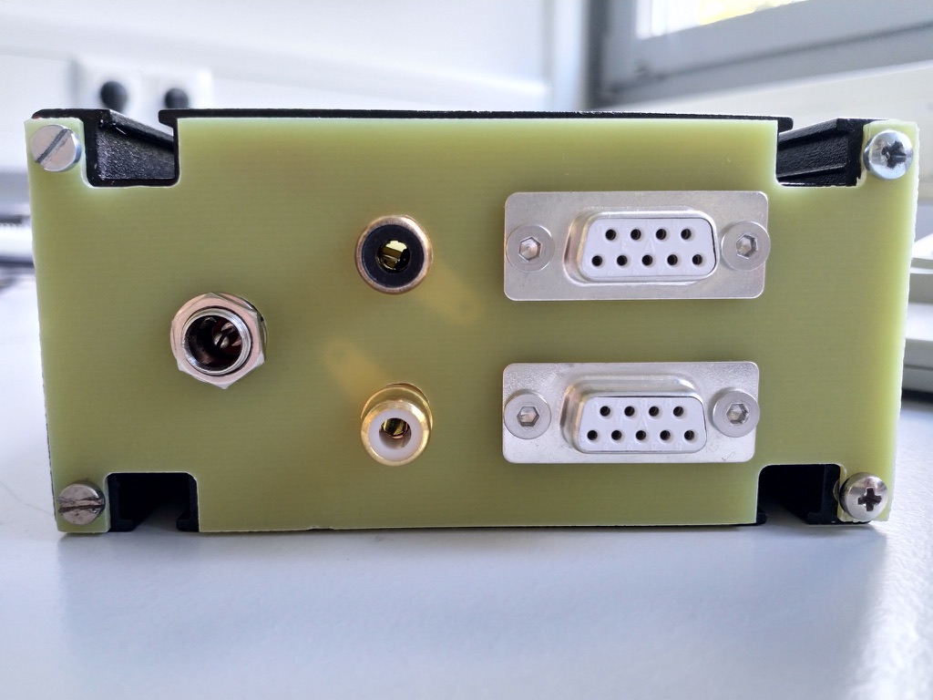
photos/measurement_box.jpeg
