aydnzn/Development-of-a-Dorsoventral-Ballistocardiographic-Measurement-System/photos/measurement_box_2.jpeg

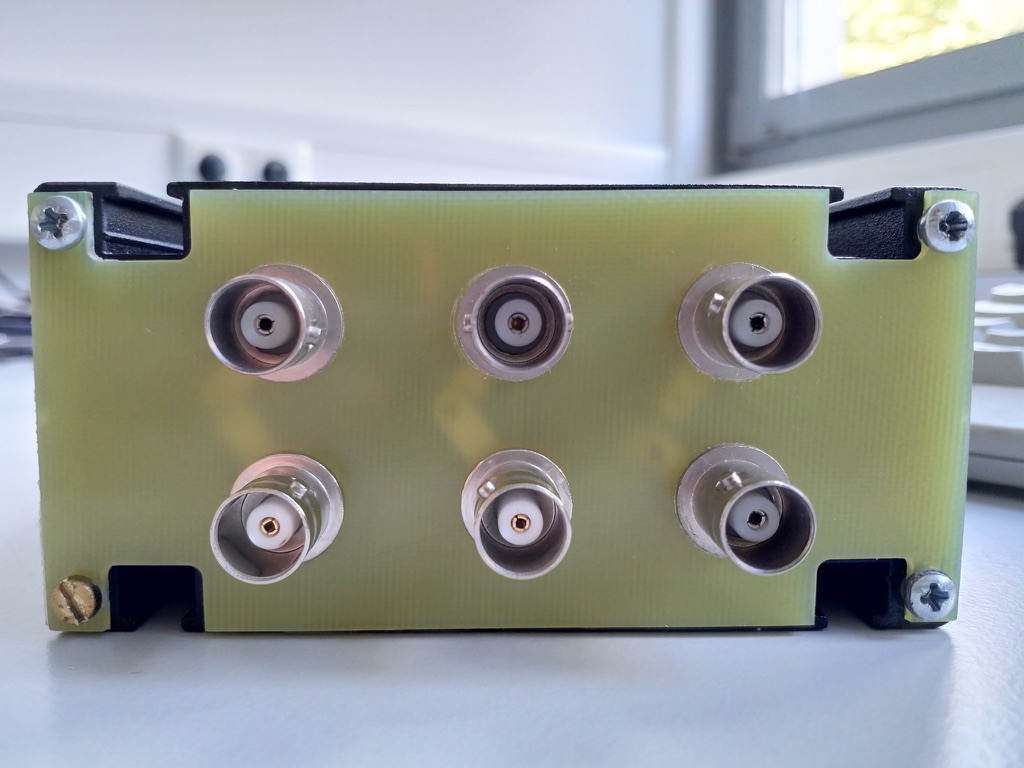
photos/measurement_box_2.jpeg
