aydnzn/Development-of-a-Dorsoventral-Ballistocardiographic-Measurement-System/photos/measurement_box_3.jpeg

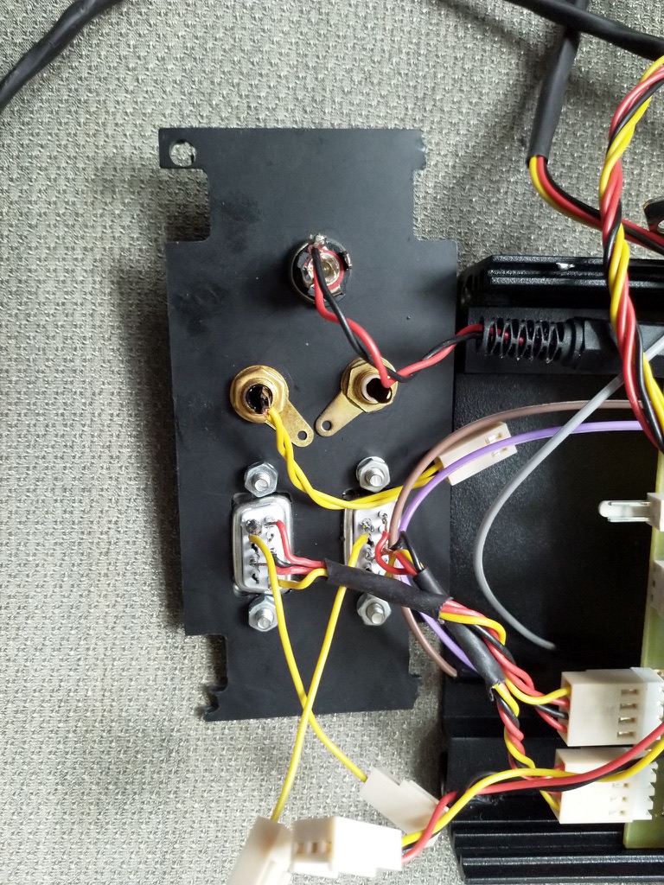
photos/measurement_box_3.jpeg
