aydnzn/Development-of-a-Dorsoventral-Ballistocardiographic-Measurement-System/photos/measurement_box_4.jpeg

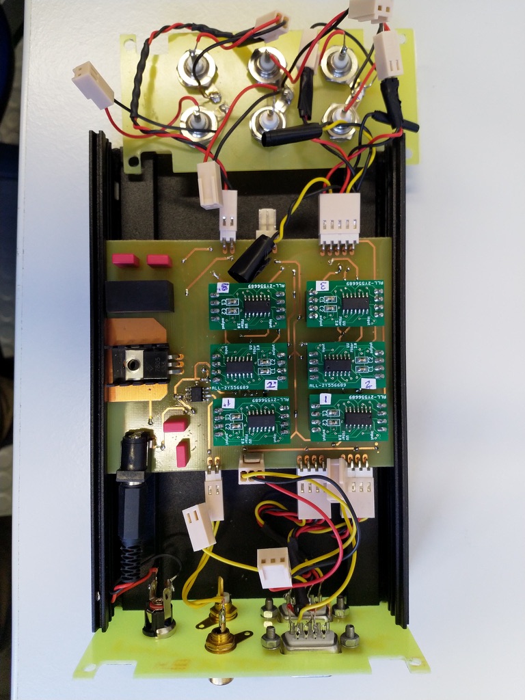
photos/measurement_box_4.jpeg
