aydnzn/Development-of-a-Dorsoventral-Ballistocardiographic-Measurement-System/photos/testing_the_sensor.jpeg

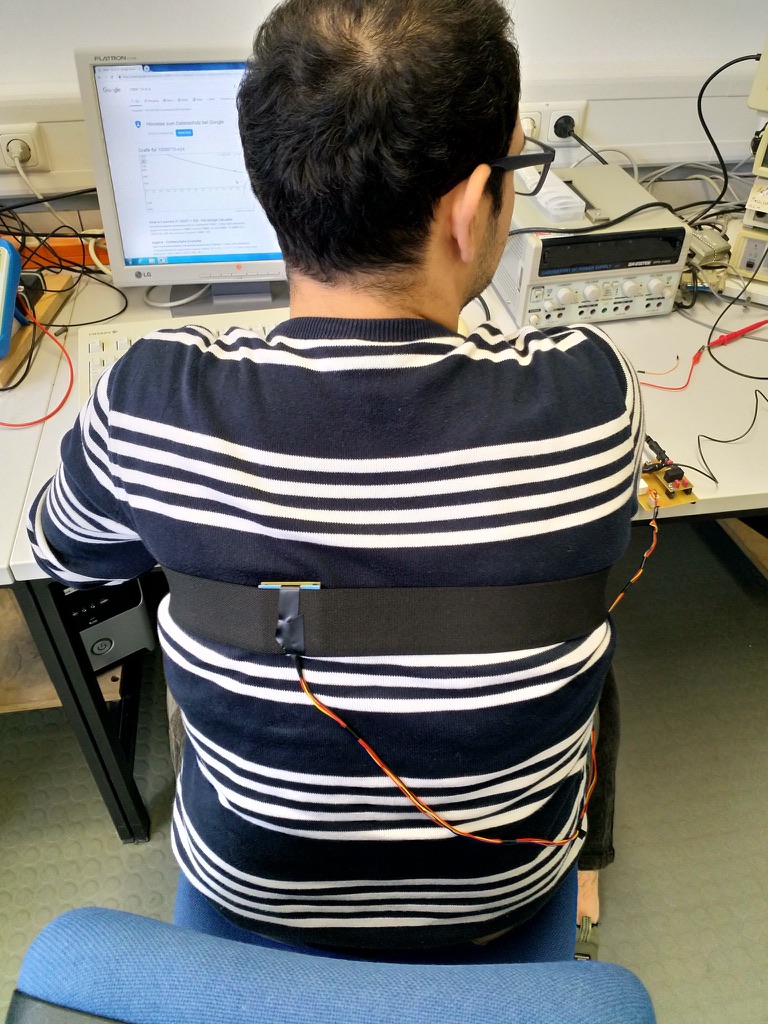
photos/testing_the_sensor.jpeg
