aydnzn/Development-of-a-Dorsoventral-Ballistocardiographic-Measurement-System/eagle_docs/v2.1/bottom.pdf

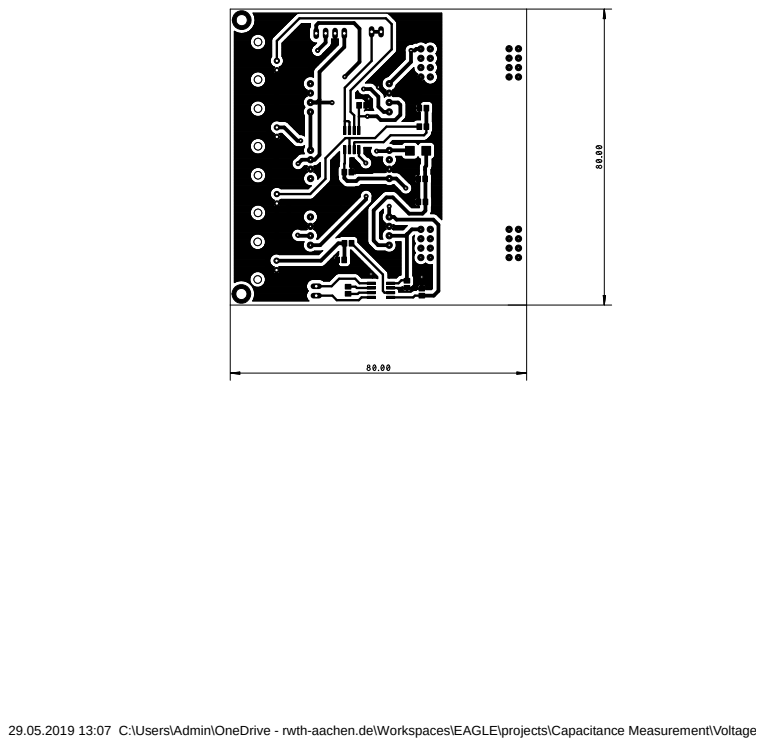
[picture p91: page 1]

29.05.2019 13:07 C:\Users\Admin\OneDrive - rwth-aachen.de\Workspaces\EAGLE\projects\Capacitance Measurement\Voltage_Divider\v2.1.brd
