aydnzn/Development-of-a-Dorsoventral-Ballistocardiographic-Measurement-System/eagle_docs/v2.1/top.pdf

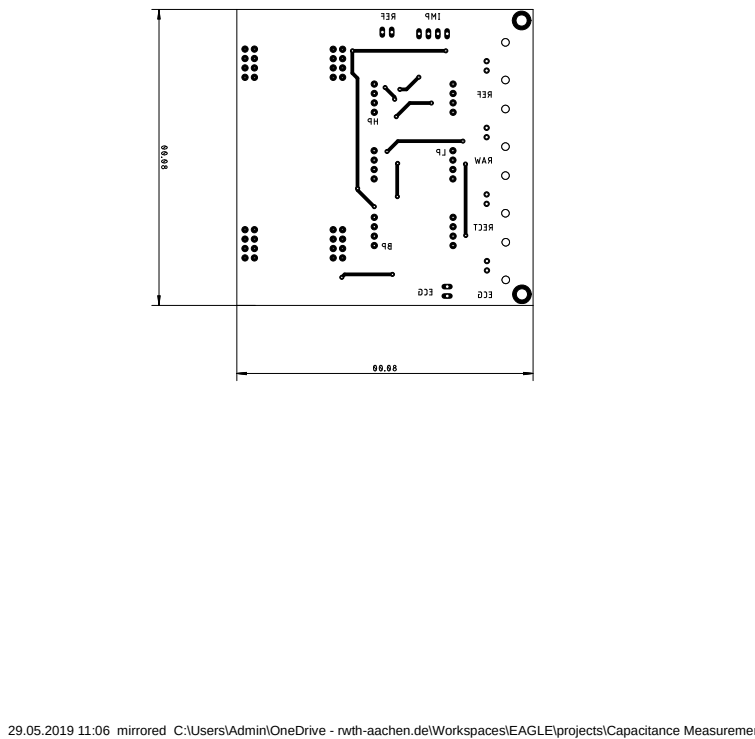
[picture p92: page 1]

29.05.2019 11:06 mirrored C:\Users\Admin\OneDrive - rwth-aachen.de\Workspaces\EAGLE\projects\Capacitance Measurement\Voltage_Divider\v2.1.brd
