aydnzn/Development-of-a-Dorsoventral-Ballistocardiographic-Measurement-System/eagle_docs/pvdf_main_board/v3.2.up.pdf

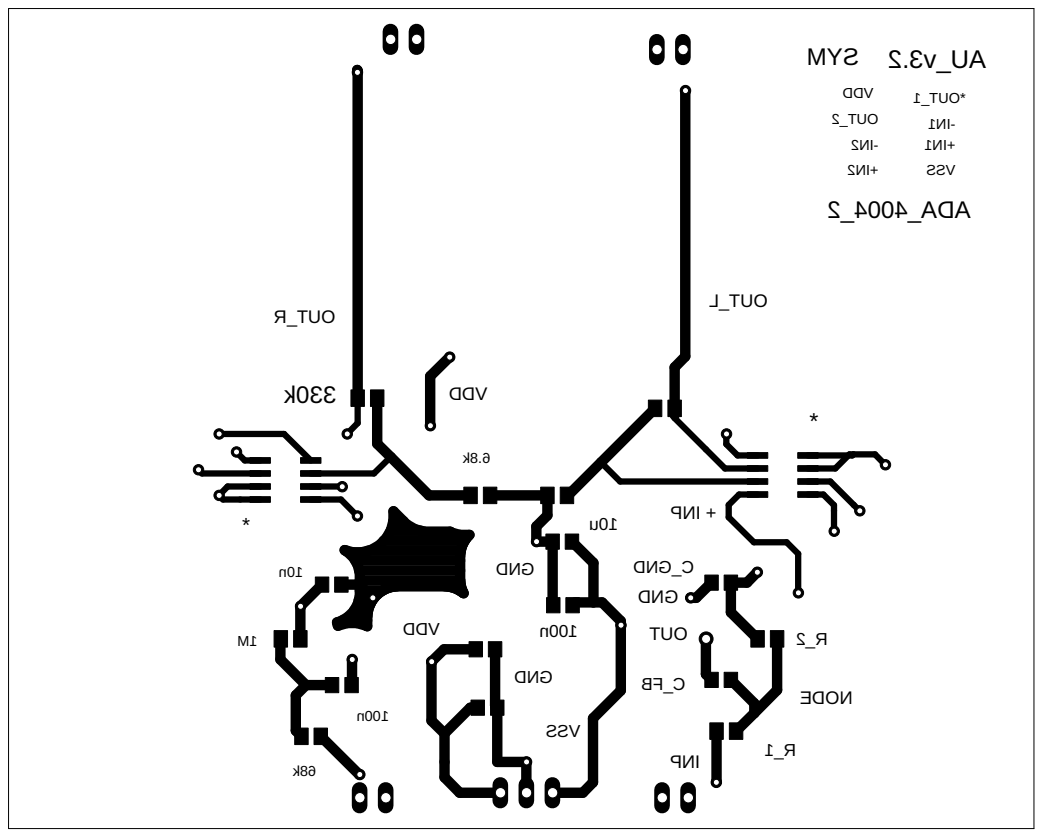
[picture p101: page 1]
