aydnzn/Development-of-a-Dorsoventral-Ballistocardiographic-Measurement-System/eagle_docs/pvdf_main_board/v3.2.up_1.pdf

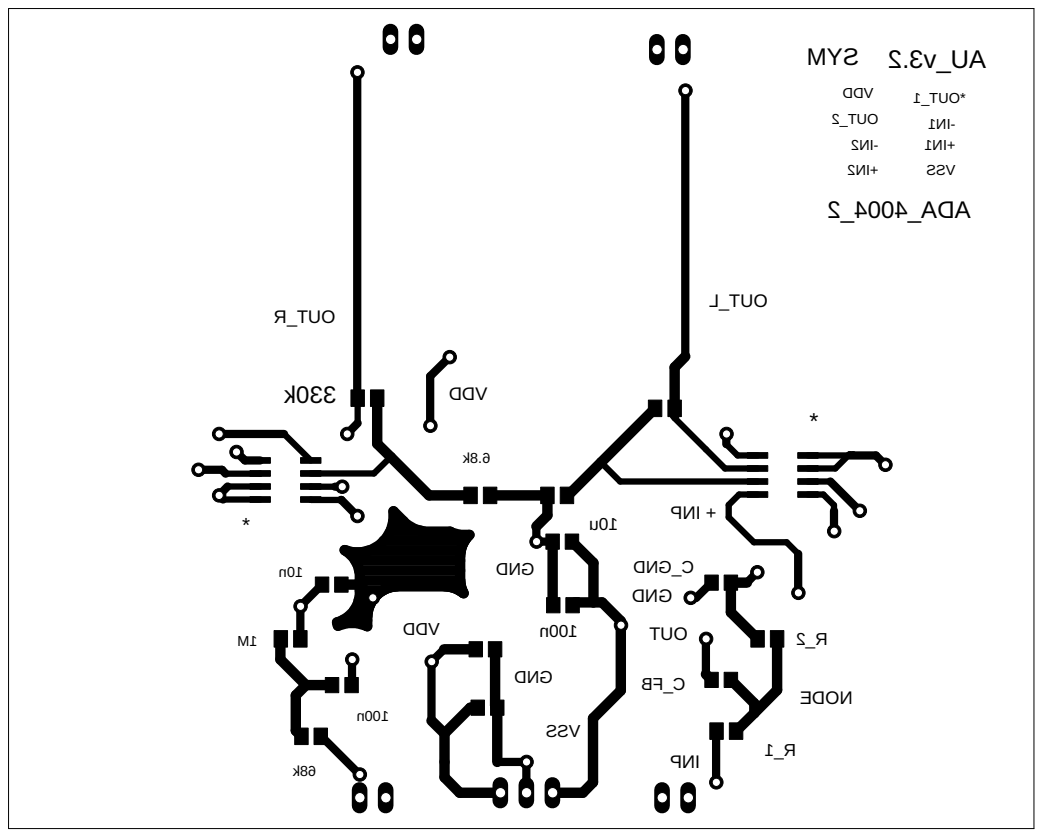
[picture p102: page 1]
