aydnzn/Development-of-a-Dorsoventral-Ballistocardiographic-Measurement-System/eagle_docs/Sensing_Unit/v1.3.pdf

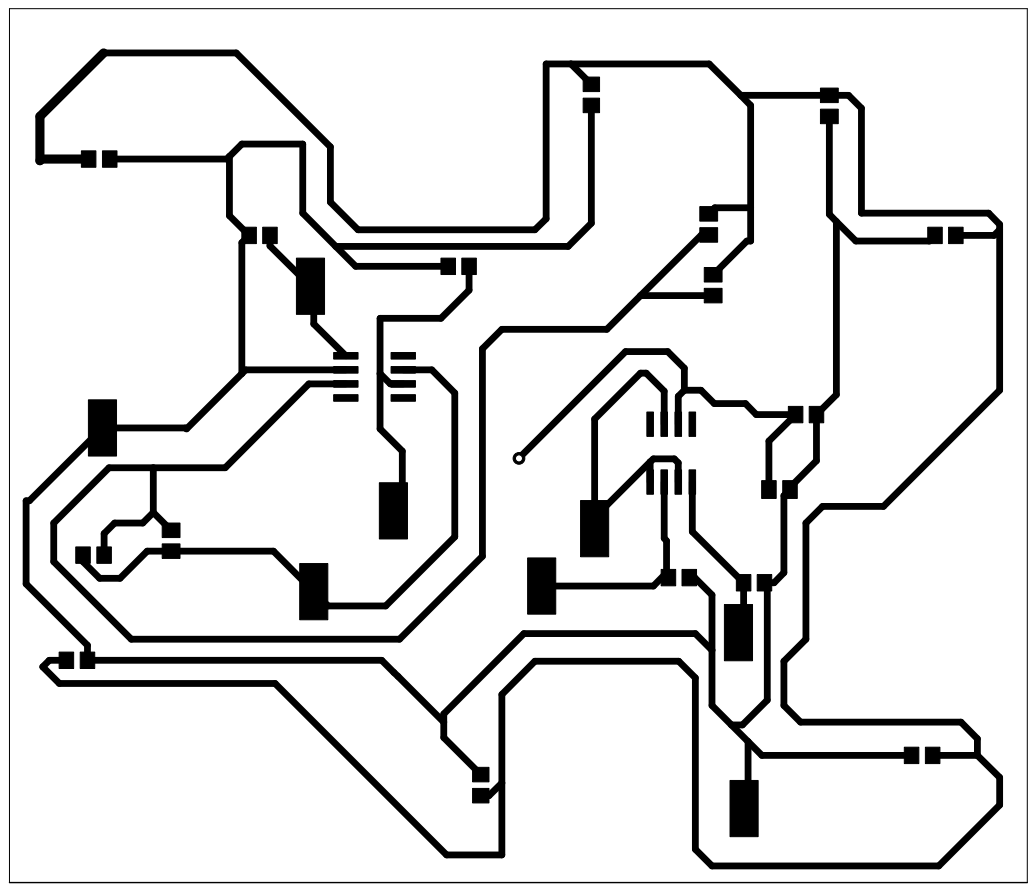
[picture p103: page 1]
