aydnzn/Development-of-a-Dorsoventral-Ballistocardiographic-Measurement-System/eagle_docs/Sensing_Unit/v1.4_bottom.pdf

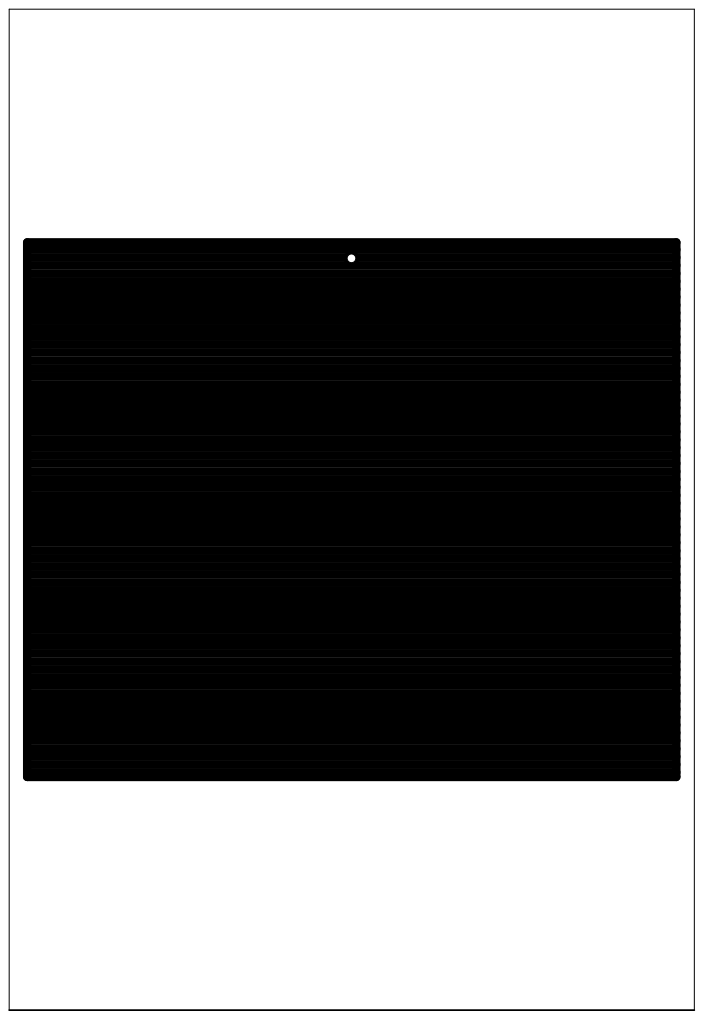
[picture p104: page 1]
