aydnzn/Development-of-a-Dorsoventral-Ballistocardiographic-Measurement-System/eagle_docs/Sensing_Unit/v1.4_top.pdf

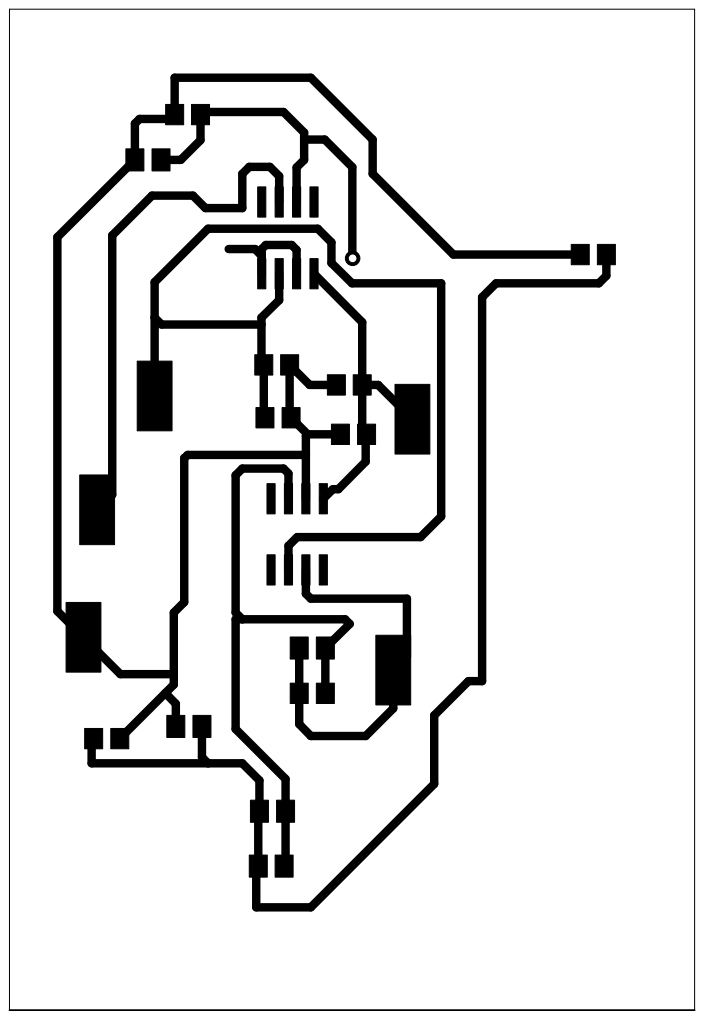
[picture p105: page 1]
