aydnzn/Development-of-a-Dorsoventral-Ballistocardiographic-Measurement-System/eagle_docs/v2.1/voltage_divider_v2.1.pdf

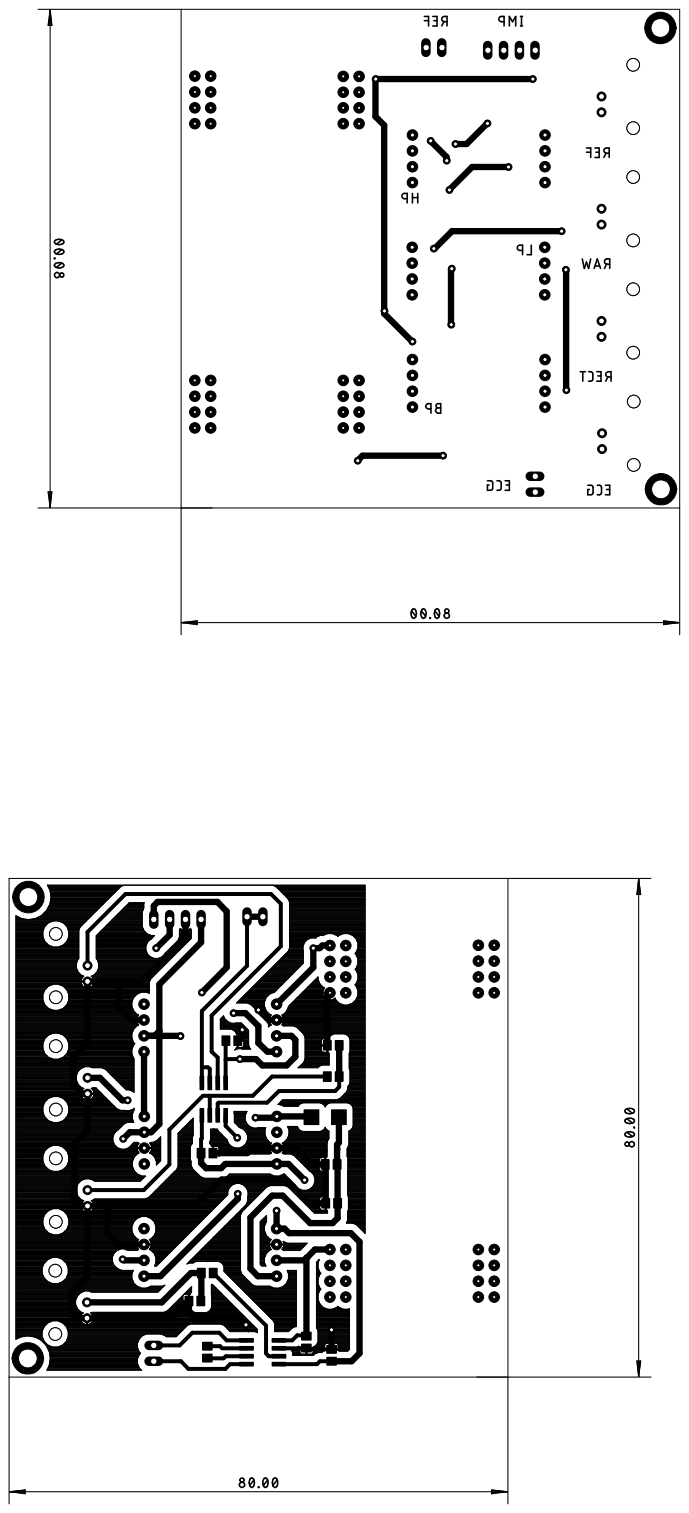
[picture p106: page 1]
