aydnzn/Development-of-a-Dorsoventral-Ballistocardiographic-Measurement-System/eagle_docs/Sensing_Unit/v1.2.pdf

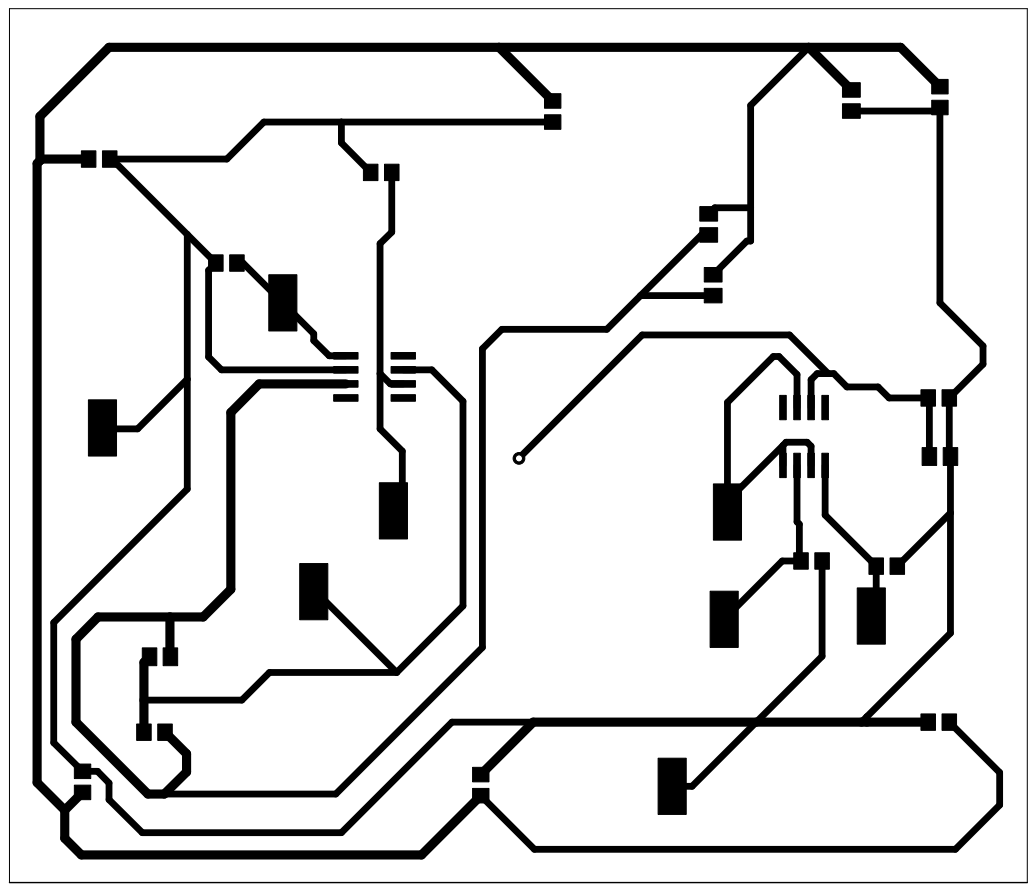
[picture p107: page 1]
