aydnzn/Development-of-a-Dorsoventral-Ballistocardiographic-Measurement-System/eagle_docs/Sensing_Unit/v1.2_bottom.pdf

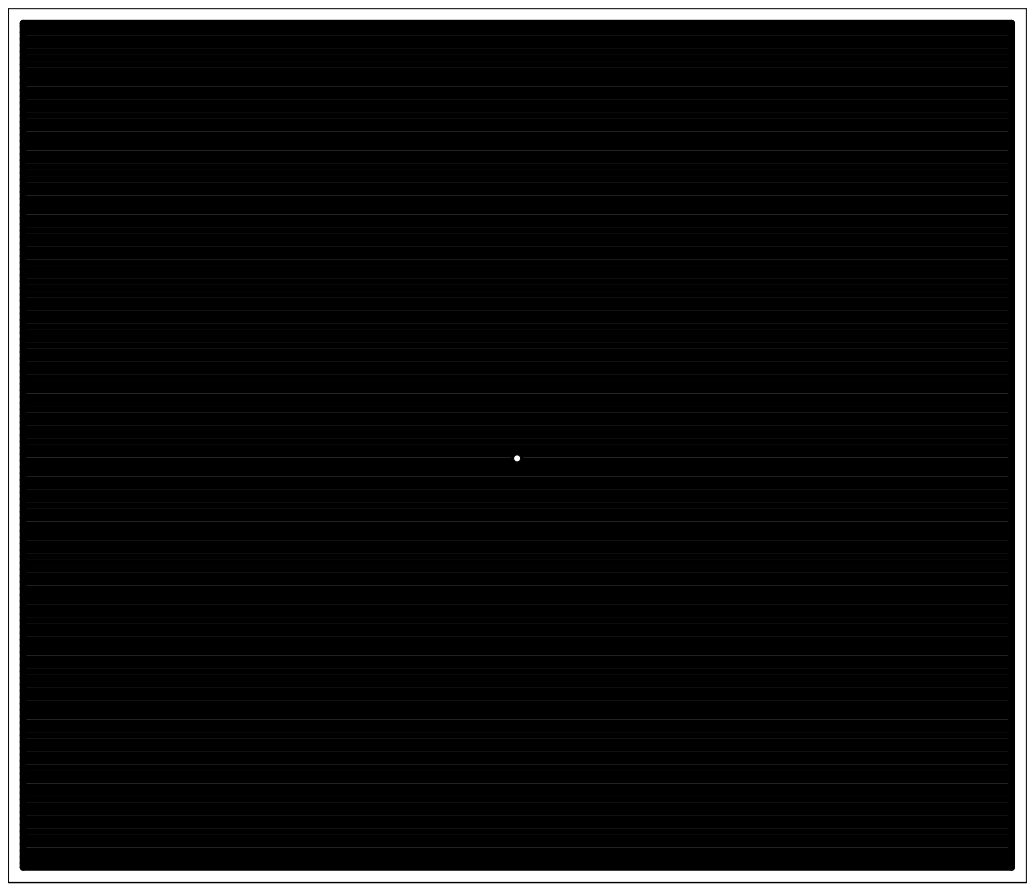
[picture p108: page 1]
