aydnzn/Development-of-a-Dorsoventral-Ballistocardiographic-Measurement-System/eagle_docs/deneme_1/fsr_electrode.brd

## EAGLE design eagle_docs/deneme_1/fsr_electrode.brd (2023-07-21)

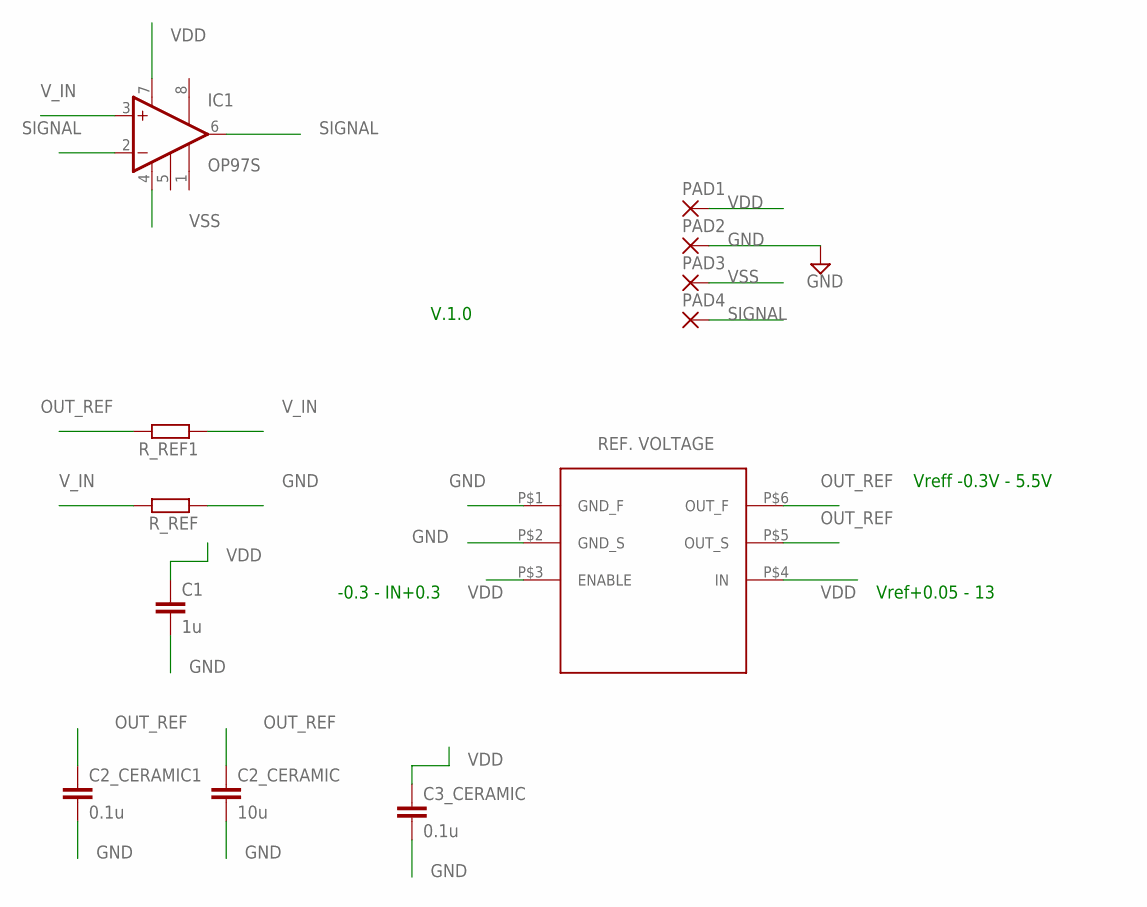
[picture p131: schematic fsr_electrode.sch]

Parts:
C1: 1u; C0805
C2_CERAMIC: 10u; C0805
C2_CERAMIC1, C3_CERAMIC: 0.1u; C0805
IC1: OP97S; SO08
PAD1, PAD2, PAD3, PAD4: SMD5; SMD2,54-5,08
REF3450: REF3450IDBVR; UZUN
R_REF, R_REF1: 10k; M0805

Connections:
GND: C1.2, C2_CERAMIC.2, C2_CERAMIC1.2, C3_CERAMIC.2, PAD2.1, REF3450.P$1 (GND_F), REF3450.P$2 (GND_S), R_REF.1
OUT_REF: C2_CERAMIC.1, C2_CERAMIC1.1, REF3450.P$5 (OUT_S), REF3450.P$6 (OUT_F), R_REF1.2
SIGNAL: IC1.2 (-IN), IC1.6 (OUT), PAD4.1
VDD: C1.1, C3_CERAMIC.1, IC1.7 (V+), PAD1.1, REF3450.P$3 (ENABLE), REF3450.P$4 (IN)
VSS: IC1.4 (V-), PAD3.1
V_IN: IC1.3 (+IN), R_REF.2, R_REF1.1

Notes on the sheet:
V.1.0
Vref+0.05 - 13
-0.3 - IN+0.3
Vreff -0.3V - 5.5V

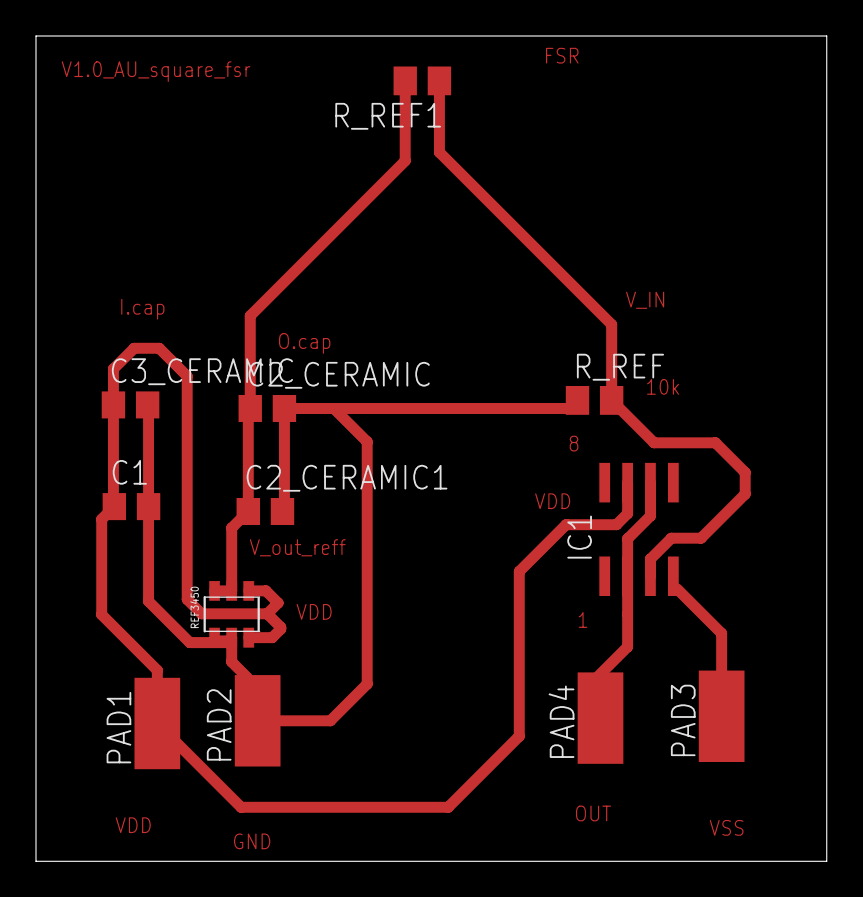
[picture p132: board fsr_electrode.brd from above]

Board: 2 copper layers, 43.9 x 45.9 mm, 12 parts (0 on the bottom side), 6 nets.
