aydnzn/Development-of-a-Dorsoventral-Ballistocardiographic-Measurement-System/eagle_docs/pvdf_sensor/v.1.0_electrode.brd

## EAGLE design eagle_docs/pvdf_sensor/v.1.0_electrode.brd (2023-07-21)

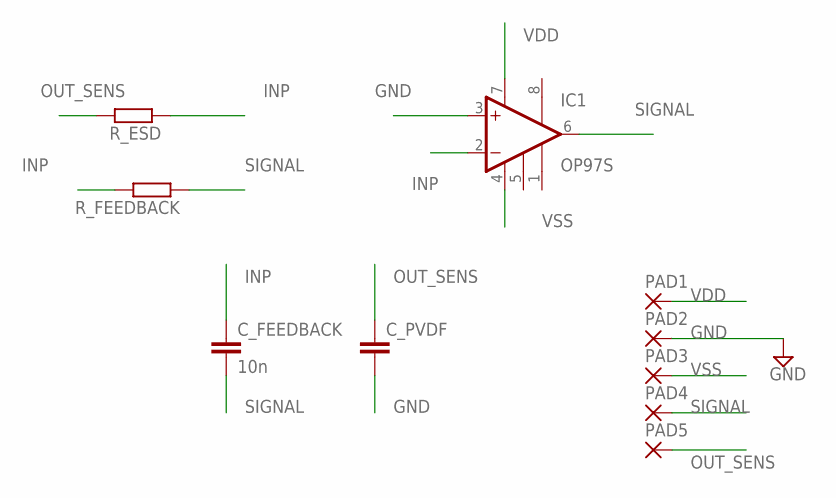
[picture p133: schematic v.1.0_electrode.sch]

Parts:
C_FEEDBACK: 10n; C0805
C_PVDF: C-EUC0805; C0805
IC1: OP97S; SO08
PAD1, PAD2, PAD3, PAD4, PAD5: SMD5; SMD2,54-5,08
R_ESD: 10k; M0805
R_FEEDBACK: 100M; M0805

Connections:
GND: C_PVDF.2, IC1.3 (+IN), PAD2.1
INP: C_FEEDBACK.1, IC1.2 (-IN), R_ESD.1, R_FEEDBACK.2
OUT_SENS: C_PVDF.1, PAD5.1, R_ESD.2
SIGNAL: C_FEEDBACK.2, IC1.6 (OUT), PAD4.1, R_FEEDBACK.1
VDD: IC1.7 (V+), PAD1.1
VSS: IC1.4 (V-), PAD3.1

Board: 2 copper layers, 10 parts (0 on the bottom side), 6 nets, no tracks yet.
